The-Open-Memory-Initiative-OMI/omi/docs/how_omi_is_engineered.md

<!-- SPDX-License-Identifier: CC-BY-SA-4.0 -->
# How OMI Is Engineered

OMI (Open Memory Initiative) is not just an open hardware project.
It is an attempt to engineer memory systems **the way they should have been engineered all along**.

This document explains:
- How OMI approaches DDR memory design
- Why the process looks "heavy" before any PCB is drawn
- What kind of contributors OMI is built for
- Why correctness, not performance, is the first milestone

If you have ever debugged a memory issue that "shouldn't happen," this is for you.

---

## The Problem with How Memory Is Usually Designed

Most memory designs fail in one of two ways:

1. **They start with schematics too early**
2. **They rely on experience instead of explicit intent**

This leads to designs where:
- Architecture is implicit
- Constraints are tribal knowledge
- Layout decisions silently redefine behavior
- Failures appear late and intermittently
- Debugging becomes guesswork

Commercial teams survive this with time, money, and iteration.
Open projects usually don't.

OMI exists to change that.

---

## OMI's Core Belief

> **Memory correctness is architectural, not procedural.**

You cannot "fix" a bad memory design with:
- better routing
- more decoupling
- aggressive calibration
- luck

You can only prevent failure by **deciding correctly early** and **preserving those decisions relentlessly**.

---

## How OMI Is Different

OMI is engineered **from the outside in**, not the inside out.

Instead of:
> schematic → layout → debug → patch

OMI follows:
> system intent → architecture → constraints → implementation → validation → hardware

Every stage exists to **protect the previous one**.

---

## The OMI Engineering Stack (High Level)

OMI is structured into explicit stages:

### Stage 1–4: System Understanding
- Why DRAM behaves the way it does
- Memory hierarchy assumptions
- DRAM internals, protocols, and physics
- Signal integrity fundamentals

No design happens here.
Only understanding.

---

### Stage 5: Architecture
- Signals are defined
- Topologies are chosen
- Constraints are declared
- Power domains are separated
- Assumptions are locked

This is where *truth is defined*.

---

### Stage 6: Implementation Translation
- Architecture becomes structure
- Blocks, interfaces, and pin groupings are defined
- Nothing new is invented
- Nothing is optimized

This stage exists so schematics cannot lie.

---

### Stage 7: Schematic Capture Discipline
- How schematics must be drawn
- How intent must be visible
- How ambiguity is prevented

This stage exists because schematics are where most designs start to rot.

---

### Stage 8: Validation & Review
- Architecture compliance checks
- Schematic correctness checks
- Constraint enforcement
- Power and failure containment reviews

If a failure cannot be explained, the design is rejected.

---

### Stage 9: Minimal Reference Schematic
- One rank
- No optimizations
- No optional features
- Fully reviewable
- Fully correct

This proves the architecture is real.

---

### Stage 10: Layout & SI/PI Guidelines
- How physics must behave
- How layout must respect architecture
- How margins are preserved

No numbers. Only intent.

---

## What OMI Is *Not*

OMI is not:
- A fastest-memory project
- A cost-optimized DIMM
- A vendor replacement
- A shortcut to production hardware

OMI is a **reference-quality foundation**.

Performance, optimization, and productization come later — on top of something solid.

---

## Who OMI Is For

OMI is for engineers who:

- Have debugged memory issues they didn't cause
- Are tired of "it works on our board"
- Care about explainability more than heroics
- Want to contribute to something *structurally correct*
- Believe open hardware deserves the same rigor as closed hardware

OMI is not beginner content.
But it is honest content.

---

## How You Can Contribute

You can contribute to OMI by:

- Reviewing architectural documents
- Challenging assumptions
- Improving clarity without adding complexity
- Extending later stages carefully
- Helping translate the reference design into variants

You don't need permission to think critically.
You do need discipline to respect the process.

---

## The OMI Promise

OMI promises that:

- Every decision is documented
- Every constraint is visible
- Every failure is explainable
- Nothing important is implicit

If OMI succeeds, it won't just produce a DIMM.

It will produce a **way of engineering memory that others can trust, reuse, and build on**.

---

## Final Thought

Most hardware projects fail quietly.
Most memory bugs are never truly understood.

OMI is an attempt to do something harder:

> **Build memory systems that make sense — even years later.**

If that excites you, welcome.
