The-Open-Memory-Initiative-OMI/omi/docs/implementations/2026-06-01-phase5-erc.md

# Phase 5 — ERC cleanup (electrical coherence, honestly)

**Date:** 2026-06-01
**Branch:** `phase5-erc` (based on `phase4-footprints`, the P4-bearing base)
**Status:** complete — **genuine ERC = 0**; J1 kept frozen (directional retype broke connectivity, reverted); PR open (not merged).
**Tooling:** `kicad-cli` 9.0.8; `powershell.exe`. Integrity ethos: **honesty over the number.**

---

## 1. Problem / Motivation

ERC = 85 (all error). The repo's audit found the project *overclaimed* (an "L1 PASS" over a
blank template). Phase 5 must not repeat that: the success criterion is **honesty, not the ERC
number.** Resolve every violation with a *real* disposition — connect what should connect,
NC-flag only genuine NCs, place the parts a functional DDR4 device requires — or leave an
explicitly-justified remainder. A faked zero is a failure.

## 2. Classification (read-only fan-out vs. the H5AN8G8NAFR-UHC datasheet / JEDEC DDR4 ×8)

The 85 are entirely on the DRAM side (8× U_DRAM0–7, identical). **The brief's assumption that
the 16 `pin_not_driven` are J1-driven address nets is incorrect** — they are the two
*unconnected input balls* (each unconnected input throws both `pin_not_connected` **and**
`pin_not_driven`):

| Ball | Signal | Type | Count | Honest disposition | Rationale |
|---|---|---|---|---|---|
| A3 | TDQS_c | Output | 8 pnc | **NC flag** | DM is enabled (A7=DM/DBI wired) → TDQS disabled → A3 RFU/NC (datasheet) |
| F2 | NC/C2/ODT1 | Passive | 8 pnc | **NC flag** | 1-rank, non-3DS → C2/ODT1 unused → genuine NC |
| G2 | NC/C0/CKE1 | Passive | 8 pnc | **NC flag** | 1-rank, non-3DS → C0/CKE1 unused → genuine NC |
| G8 | NC/C1/~CS1 | Passive | 8 pnc | **NC flag** | 1-rank, non-3DS → C1/CS1 unused → genuine NC |
| L9 | ~ALERT | Open collector | 8 pnc | **NC flag** | open-drain error output, parity/CRC unused in v1 → may float (host-side J1 ALERT_n also NC per P3) |
| G9 | TEN | Input | 8 pnc + 8 pnd | **tie → VSS** | connectivity-test-enable input must be held low for normal operation (never float) |
| N3 | PAR | Input | 8 pnc + 8 pnd | **tie → VSS** | rigorous C/A-parity disable (don't float a CMOS input); host-side J1 PARITY stays NC per P3 |
| B9 | ZQ | Passive | 8 pnc | **240 Ω → VSS resistor** | JEDEC-mandatory output-driver/ODT calibration resistor (RZQ); a real defect, never NC |

Counts: 40 NC flags (A3,F2,G2,G8,L9 ×8) + 16 VSS ties (G9,N3 ×8, clears 16 pnc + 16 pnd) + 8 ZQ
resistors (clears 8 pnc) = the 64 pnc and 16 pnd.

**5 `power_pin_not_driven`** (no `power_output` exists anywhere today — all J1 power pins are
`passive`): VDD (#PWR01), VPP (#PWR03), GND (#PWR07), VDDSPD (U_SPD0 VCC) — **J1 carries each**;
and VDDQ (U_DRAM B2) — **J1 has no VDDQ pin** (a DDR4 edge has VDD, not VDDQ).

## 3. Plan (each step validated; commit incrementally)

1. **Directional J1 (controlled symbol change — types only):** update the generator with a
   deterministic direction rule (NC→`no_connect`; CA_CLK→`output`; DQ_DQS→`bidirectional`; SPD
   SCL/SDA→`bidirectional`, SA0-2→`output`; POWER→see below), regenerate `omi.kicad_sym`, and
   update the edge sheet's **embedded** lib_symbols copy (kicad-cli reads the embedded copy).
   **Re-verify 288 pins still exact-match the CSV (number+name); only types change.**
2. **Power drive:** J1's multi-pin power rails (27 VDD / 92 GND / 5 VPP / 2 VTT) cannot all be
   `power_output` without multiple-power-output conflicts, so power is sourced by **one
   `PWR_FLAG` per rail** (VDD, VPP, GND, VDDSPD) — the idiomatic "supplied off-board through the
   edge" marker. *(Empirically confirmed during execution; J1 power pins stay `passive`.)*
3. **VDDQ → VDD:** merge the local `/address-command-clock/VDDQ` net into global VDD (on a DDR4
   UDIMM VDD≡VDDQ, bridged on-module) so VDD's source drives it. Clears the VDDQ item.
4. **ZQ resistors:** add one 240 Ω 0402 resistor per DRAM (R1–R8), ZQ(B9) → R → GND, each
   footprinted `Resistor_SMD:R_0402_1005Metric` (preserves P4's 100% footprint coverage; BOM
   updates). Clears 8 pnc.
5. **TEN + PAR ties:** global label `GND` on G9 (TEN) and N3 (PAR) of each DRAM (16). Clears
   16 pnc + 16 pnd.
6. **NC flags:** `no_connect` on A3, F2, G2, G8, L9 of each DRAM (40). Clears 40 pnc.

All DRAM-pin edits are placed at computed pin endpoints (`sheet = placement + (px, −py)`; all 8
DRAMs are at rotation 0, no mirror) via a stdlib-only P5 helper.

## 4. Integrity stance (the hard rule)

- **ZQ is placed, never NC-flagged** — a functional DDR4 device requires the 240 Ω resistor.
- **TEN and PAR are tied to VSS, not floated** — unused CMOS inputs get a defined level.
- **Only genuine NCs are NC-flagged** (TDQS_c with DM enabled; the 3DS/2nd-rank balls; the
  unused open-drain ALERT output) — each datasheet-backed.
- Nothing a functional module would connect is silenced to hit zero. Any residual is documented
  per-item.

## 5. What Changed

| File | Change | Description |
| --- | --- | --- |
| `tools/edge_symbol/gen_edge_symbol.py` | modified | Add the directional pin-type rule (types only; number+name stay CSV-exact). |
| `design/power/omi_v1_power/omi.kicad_sym` | regenerated | Directional pin types; 288 pins still exact-CSV. |
| `design/power/omi_v1_power/udimm-edge-interface.kicad_sch` | modified | Embedded J1 lib_symbols copy retyped to match. |
| `design/power/omi_v1_power/address-command-clock.kicad_sch` | modified | PWR_FLAGs (VDD/VPP/GND); VDDQ→VDD; 8 ZQ resistors; 16 VSS ties; 40 NC flags. |
| `design/power/omi_v1_power/spd-and-configuration.kicad_sch` | modified | PWR_FLAG on VDDSPD. |
| `build/p5/*` | added | Per-step ERC/netlist evidence; symbol re-verify; ERC-resolution ledger. |

Untouched: the CSV, `validation/**`, `docs/08…/scripts/**`, the `.kicad_pcb`.

## 5a. Directional J1 — attempted, reverted (the documented frozen-J1 alternative)

The directional retype was implemented in the generator and applied (signals→output/bidirectional,
power→power_output) — number+name stayed CSV-exact (diff: only type tokens changed). But it
**disconnected J1 from every one of its nets** (netlist-verified: `D0_DQ0` collapsed to
`{U_DRAM0}`, `A0`/`VDD`/`GND` lost J1), spiking ERC to 210. Root cause: this design anchors a
`global_label` directly on each J1 pin with **no wire** (the P2 generator's design); KiCad's
label-on-pin connection holds for `passive` pins but **not** once the pin becomes a directional
driver. Rather than silently break connectivity, J1 was **kept frozen (passive)** and reverted
in full (generator, `omi.kicad_sym`, embedded copy) — the brief's documented frozen-J1
alternative. Power is therefore sourced by PWR_FLAGs (§ below), and the 16 `pin_not_driven`
turned out to be the unconnected TEN/PAR inputs (not J1-driven nets, as the brief had assumed),
cleared by the VSS ties. No directional change ships.

## 6. Verification — ERC-resolution ledger (original 85 → resolution)

| Original violation | Count | Resolution | Honest? |
|---|---|---|---|
| `pin_not_connected` A3 (TDQS_c), F2/G2/G8 (3DS+2nd-rank), L9 (ALERT) | 40 | `no_connect` flags | genuine NC (datasheet: DM enabled→TDQS off; 1R non-3DS; unused open-drain) |
| `pin_not_connected` G9 (TEN), N3 (PAR) | 16 | global-label **VSS tie** | unused CMOS inputs tied to their inactive level (not floated) |
| `pin_not_driven` G9 (TEN), N3 (PAR) | 16 | (same VSS ties) | TEN held low; PAR is the proper C/A-parity disable |
| `pin_not_connected` B9 (ZQ) | 8 | **240 Ω→VSS resistor** (R1–R8, R_0402) | JEDEC-mandatory RZQ; a real defect — placed, never NC'd |
| `power_pin_not_driven` VDD/VPP/GND/VDDSPD | 4 | one **PWR_FLAG** per rail (J1 = off-board source) | idiomatic "supplied off-board" |
| `power_pin_not_driven` VDDQ | 1 | **merge VDDQ→VDD** (8 locals→global) | DDR4 VDD≡VDDQ, bridged on-module |
| **Total** | **85** | → **ERC = 0** | nothing a functional module would connect was silenced |

**Invariants re-confirmed:** generator `--verify` = **288/288 pins exact-match the CSV**;
`omi.kicad_sym` + `tools/edge_symbol/**` + the CSV + the `.kicad_pcb` + `validation/**`
**byte-untouched** (the only schematic file changed is `address-command-clock.kicad_sch`).
**Footprint completeness:** 18/18 real components footprinted (J1, 8 DRAM, SPD, **8 new ZQ
resistors** at `Resistor_SMD:R_0402_1005Metric`); `#PWR*`/`#FLG_*` carry none (correct).

**Connectivity sanity (final netlist):** `D0_DQ0`={J1,U_DRAM0}; `CK_t`={J1,8 DRAM};
`VDD`=139 nodes (incl. ex-VDDQ balls); `GND`=224 (incl. R1–R8 + TEN/PAR ties + SPD);
`ZQ0`={R1,U_DRAM0}; `SPD_SCL`/`VDDSPD`={J1,U_SPD0}; U_DRAM0 G9/N3→GND, B9→ZQ0, A3→NC. No net
split or accidental merge.

**Integrity self-audit:** the only `no_connect` flags placed are on datasheet-genuine NC balls
(TDQS_c with DM enabled; 3DS stack-ID + 2nd-rank balls; the unused open-drain ALERT output).
ZQ was placed (not NC'd); TEN/PAR were tied (not floated/NC'd). Nothing a functional module
would connect was silenced to reach zero. No REVIEW items remained unresolved.

## 7. Remaining (handoff)

- **P6:** export pipeline (netlist + BOM + PDFs) — now electrically coherent + footprint-complete.
- **P7:** honest README/claims (carry the J1 mechanical caveat + this phase's honest framing).

## 8. Related Docs

- `PHASE5_ERC_BRIEF.md` (authoritative spec, untracked).
- `docs/implementations/2026-06-01-phase4-footprints.md` (footprints).
- `docs/implementations/2026-06-01-phase2-edge-symbol.md` (the J1 symbol generator this modifies).
