The-Open-Memory-Initiative-OMI/omi/docs/01_dram_fundamentals/destructive_reads.md

# Destructive Reads: Why Reading DRAM Alters Its State

This document explains **why reading DRAM is inherently destructive**, how this behavior shapes timing constraints, and why correct restoration is essential for system reliability.

Destructive reads are one of the most important differences between DRAM and other memory technologies.

---

## What "Destructive Read" Means

In DRAM, a read operation does not merely observe stored data.

It **changes the physical state** of the memory cell.

Specifically:

- Reading a DRAM cell discharges or redistributes its stored charge
- The original data is disturbed in the process
- The cell must be rewritten to preserve correctness

This behavior is fundamental to DRAM operation.

---

## Why Reads Are Destructive

DRAM cells store data as extremely small amounts of charge.

When a row is activated:

- Each cell connects to a bitline
- Charge flows from the capacitor to the bitline
- The voltage difference is sensed and amplified

This process necessarily:

- Draws charge out of the cell
- Collapses the original stored state

There is no way to sense the charge without disturbing it.

---

## Sense Amplifiers as Restorers

Sense amplifiers serve a dual role:

1. Detecting the stored value
2. Restoring the value back into the cell

Once amplification occurs:

- The sensed value is driven strongly
- The capacitor is recharged or discharged fully
- The original data is rewritten

This restoration happens **while the row remains active**.

---

## Why Timing Matters During Restoration

Restoration is not instantaneous.

It requires:

- Sufficient time for amplification
- Stable power and reference voltages
- Minimal noise and disturbance

If timing is shortened:

- Restoration may be incomplete
- Charge levels may be marginal
- Data may decay faster than expected

Errors may not appear immediately.
They may surface minutes or hours later.

---

## Relationship to Precharge

After a row is accessed:

- It must be closed (precharged)
- Bitlines must return to a neutral state
- Cells must be isolated again

Precharge is required to:

- Prepare the array for the next activation
- Prevent interference between rows
- Maintain charge integrity

Skipping or shortening precharge corrupts data.

---

## Why Partial Reads Are Not Possible

Because an entire row is activated:

- All cells in the row are disturbed
- Even if only a few columns are read

This means:

- Every read is effectively a read-modify-write operation
- Restoration happens for the entire row
- Timing parameters must protect all cells

This is why DRAM accesses are fundamentally row-based.

---

## Interaction with Refresh

Refresh and reads are closely related.

- A refresh operation is effectively an internal read and restore
- Normal reads also perform restoration
- Both depend on the same physical mechanisms

Incorrect read timing affects refresh reliability, and vice versa.

---

## Why Errors Can Be Delayed

A destructive read error may:

- Slightly under-restore charge
- Leave data barely within margin
- Pass immediate verification

But:

- Subsequent leakage accelerates decay
- Later reads observe corrupted data
- Failures appear disconnected from cause

This delayed manifestation makes debugging extremely difficult.

---

## Implications for DDR Timing Parameters

Several DDR timing parameters exist **solely** because reads are destructive:

- Row active time (ensuring full restoration)
- Precharge time (ensuring safe isolation)
- Activate-to-read delays
- Read-to-precharge constraints

These timings protect data integrity, not performance.

Violating them risks silent corruption.

---

## Why This Matters for Module-Level Design

At the module level:

- Signal integrity affects sensing accuracy
- Power noise affects amplification
- Timing skew affects restoration completeness

Design margins exist to ensure destructive reads do not become destructive failures.

OMI documents these relationships explicitly.

---

## Why Destructive Reads Are Often Ignored

Many engineers never encounter this concept because:

- DRAM abstracts it away
- DDR protocols enforce safety automatically
- Failures are rare and silent

But ignoring it leads to:

- Misinterpretation of timing rules
- Overconfidence in marginal designs
- Fragile systems

---

## Takeaway

DRAM reads are not passive.

Every read:

- Destroys stored charge
- Relies on precise restoration
- Depends on timing, power, and signal quality

Correct memory operation exists only because these destructive effects are carefully controlled.

OMI exists to make those controls visible and understandable.
