The-Open-Memory-Initiative-OMI/omi/CHARTER.md

<!-- SPDX-License-Identifier: CC-BY-SA-4.0 -->
# The Open Memory Initiative (OMI) 

#  An Open, Community-Built DDR Memory Initiative

## 1\. Executive Summary:

While modern computing systems depend on DRAM, memory in particular is still one of the most closed and least understood parts of a system’s system stack. Even though processors and toolchains (and perhaps accelerators) are moving in a positive direction in open-source terms and making meaningful headway, system memory is yet to become commonplace with obscure designs, lack of knowledge, as well as a barrier to independent implementation being among the top reasons behind it. That has bred a structural imbalance. Open CPUs and open systems continue to rely on closed memory. Education focuses on using memory rather than understanding or building it. AI-driven demand and supply constraints, alongside market prioritization, have revealed the fragility and centralization of the memory ecosystem.

The OMI Project attempts to fill this gap. OMI is a community-driven initiative to develop open, reproducible, and manufacturable DDR memory module design from mature DDR technology, building upon PC DIMMs. Initially, a complete approach toward module-level design is accomplished, i.e. schematics, PCB layouts, documentation, and validation methodology before any chip-level DRAM design. 

OMI is a very strict definition of openness. All design artifacts and documentation, test procedures, and decision rationales must be publicly available. No closed IP, NDA-gated knowledge, or black-box components are allowed. If a design cannot be studied, reproduced, and independently verified, it fails to meet the criteria. The initial scope is deliberately limited. 

OMI v1 aims to develop a single, well-documented DDR module that can be constructed and tested on classical PC hardware. Success is not defined by performance leadership or commercial adoption, but by reproducibility, clarity, and independent verification. 

OMI is not marketed as a direct competitor to those memory makers. It is an enabler which closes the gap from open computing stack to repair the knowledge gap, and form the basis for future research, education, and experimental work. The project is successful only when many can use it and continue to build on it without permission from someone else.

## 2\. The Problem:

Why Memory Is Gatekept. DRAM is crucial to modern-day computing, yet it is still one of the least accessible and opaque technologies in the semiconductor industry. No, it’s not a coincidence of complexity. It is the result of intentional structural decisions that concentrate knowledge, capacity, and power in the hands of very few actors.

### 2.1 Market Concentration and Artificial Scarcity:

The world’s DRAM market is dominated by a tiny number of manufacturers. This sort of concentration builds a brittle ecosystem where supply decisions are also centralized, opaque, and governed by the whims and preferences of few; not the general computing community. In recent years, we have observed:

Repeated shortages of DRAM which have nothing to do with physical manufacturing limitations. Uncorrelated price volatility regardless of raw material and process changes. The systematic prioritization of high-margin markets, for example, AI accelerators and data centers. Consumer PCs, developer machines, and education platforms are deprioritized. Such dynamics have real impacts. Developers, students, researchers, and independent builders experience increasing costs and declining access to a component crucial to basic computing in the modern era. That scarcity here is not only technical. It has an organizational dimension.

### 2.2 Closed IP and Licensing Barriers:

Although DDR standards are officially published, participation in DRAM design is significantly stymied by a complex interplay of intellectual property and licensing constraints. Key barriers include: Critical implementation details obscured by NDAs. References available exclusively as proprietary designs without public access. Patent portfolios that render independent implementation legally risky. Toolchains and validation flows accessible only through commercial agreements. So “open” tends to mean: You can interpret the specification. You may not build from it. That leads to a one-way dependency; where engineers are trained to consume memory, integrate memory, and optimize around memory, but not to design memory.

### 2.3 Knowledge Hoarding in DRAM Design:

The knowledge on the design of DRAM does not flow freely through universities, open literature, or community projects. Rather, it is siloed within companies and protected as a competitive advantage. This leads to: A growing disconnect between academia and industry. Little publicly available, end-to-end DRAM design cases. Lack of open reference implementations. A dwindling body of engineers who see memory beyond the interface level. The result is structural fragility. When knowledge fails to trickle down, systems become dependent on institutions rather than understanding.

### 2.4 The Consequence: A Broken Feedback Loop:

In healthy engineering ecosystems: Knowledge is transmitted from the industry to education. Education creates new engineers. Engineers develop alternatives and new possibilities. This loop has been broken by today's memory ecosystem. Without open memory:

Open CPUs remain incomplete. Closed components still power open systems. Hardware education continues to be abstract. Innovation remains centralized. This is not sustainable for open computing, long-term resilience, or technological sovereignty.

## 3\. Why Open-Source RAM Is Necessary Now:

Open-source hardware is no longer experimental. It’s already redesigning CPUs, accelerators, interconnects, and full system-on-chip ecosystems. But memory, the bedrock of all computation, remains closed. This has turned into an asymmetry that is structural. The need for open-source RAM is no longer theoretical or aspirational. It is immediate.

### 3.1 Open Computing Cannot Exist Without Open Memory:

Open instruction sets and open processor designs have been demonstrated in the past decade as viable. Open CPUs have been built, verified, and shipped at scale by communities and companies. However, these systems still use opaque memory components.

Without open memory:

Open CPUs remain dependent on closed subsystems. Transparency at the system level is broken at the most fundamental layer. Debugging, optimization, and education stop at the memory interface. An open system will not ever be open if its most central aspect is not being studied, modified, or rebuilt. Open-source RAM is not an addendum to open hardware, it’s an essential prerequisite.

### 3.2 AI-Driven Demand Has Exposed Structural Fragility:

The exponential growth of AI workloads has tilted global DRAM allocation toward an almost exclusive user pool of high-margin customers. This has worsened existing vulnerabilities in the memory supply chain.

The impacts are already felt:

* Consumer and developer hardware is deprioritized. Prices and availability rise and fall unexpectedly. Memory becomes a strategic resource rather than a commodity.  
* When a foundational technology runs into strategic scarcity, openness is no longer a philosophical position; it is a strategy for resilience.

Open memory designs create:

1. Alternatives to centralized supply decisions.   
2. Transferable knowledge to other regions and institutions.   
3. The possibility of localized or diversified manufacturing.

### 3.3 Education and the Disappearance of Memory Expertise:

Memory systems are extensively taught at the interface and almost never at the actual implementation level.

Today most engineers graduate armed with used DDR memory, Tuned memory controllers and Modeled memory performance.

But having never designed a memory module or understood real signal integrity constraints. Worked through validation and bring-up…

This is not because there is no interest or capability in these areas. It is due to lack of access. An open source RAM project would restore the missing educational layer: actual, buildable, inspectable hardware.

### 3.4 Timing: Why This Is the Right Moment:

Three conditions now exist in parallel:

1. Mature DDR generations. DDR3 and DDR4 are widely supported, stable, and well understood.  
2. Open hardware momentum. PCB manufacturing, toolchains, community collaboration, etc. are more accessible than ever.  
3. Clear system-level demand. Developers, academics, and trainees all need transparency, not just performance.

A combination of these factors makes an open RAM project both practical and meaningful. This is not to disturb cutting-edge DRAM manufacturing. It is an assertion of re-establishing awareness at an elemental level.

### 3.5 This Is Not About Competing. It Is About Completing:

OMI is positioned not to compete with other producers. Instead, it exists to complement open CPUs. Strengthen open systems. Extend the network of engineers who have a profound understanding of memory.   
The objective is not to compete with industry. The point is to make memory no longer a single point of opacity in otherwise open systems.

## 4\. Design Philosophy & Core Principles:

OMI not only builds what it builds, but how it builds in addition to why. The following principles are non-negotiable. These are meant to safeguard the project from dilution, disunity, and quiet closure.

### 4.1 Openness Is a Technical Requirement, Not a Preference:

In this project, “open” has a strict meaning.

All artifacts necessary to comprehend, reproduce, validate, and adapt to the system must be publicly available. This includes, but is not limited to:

1. Electrical schematics  
2. PCB layouts and stack-ups  
3. Bill of materials  
4. Design constraints and assumptions  
5. Test methods and validation results  
6. Design dialogues and rationale of decisions

If a component or process cannot be documented without violating an NDA, it does not belong in the OMI stack. 

Partial openness is not openness\!\!\! 

Documentation without buildability is not openness\!\!\!

### 4.2 No Black Boxes:

They explicitly reject black boxes.

Any element that requires:

1. Trust without verification  
2. Vendor-only knowledge  
3. Undisclosed internal behavior

is incompatible with this project’s objectives.

All design decisions should be explainable\! All interfaces must be traceable\! Every limitation must be documented\! Complexity is acceptable. Opacity is not\!

### 4.3 Engineering First, Hype Last:

OMI values correctness, reproducibility, and clarity over speed, marketing, or perceived innovation.

This means:

1. Working hardware matters more than announcements  
2. Measured results matter more than projections  
3. Failed experiments are documented, not hidden  
4. The project advances through evidence, not persuasion.

### 4.4 Buildable by Others:

A design that only its creators can build has failed. All OMI outputs must satisfy the following condition:

A competent engineer, with access to standard tools and public documentation, must be able to reproduce the design and results.

This principle governs; Component selection, Manufacturing assumptions, Testing environments and documentation depth.

If a design cannot be independently rebuilt, it is incomplete\!

### 4.5 Incremental, Layered Progress:

OMI progresses in deliberate layers:

1. Understanding  
2. Documentation  
3. Design  
4. Validation  
5. Iteration

Skipping layers introduces hidden debt.  
Each layer must stand on its own before moving forward.

This approach favors long-term stability over short-term progress.

### 4.6 Decisions Follow Evidence, Not Authority:

Design decisions are justified on technical grounds — not seniority, affiliation, or assertion.

Decisions are made based on:

1. Technical merit  
2. Evidence  
3. Reproducibility

A decision stands because it can be defended and reproduced, not because of who made it.

### 4.7 Transparency Includes Limitations:

OMI documents not only what works, but also:

1. What does not work  
2. What is not yet understood  
3. What remains unresolved

Uncertainty is treated as engineering data, not weakness.

## 5\. Why Start with PC DDR Memory:

OMI starts with PC DDR memory by design, not convenience. The decision is made to strike a conscious balance between technical feasibility, community accessibility, and real-world impact. Beginning elsewhere would prolong execution indefinitely or limit it to a select group of specialists.

### 5.1 Why DDR (and Not SRAM, HBM, or LPDDR):

Dynamic RAM is the dominant form of main memory in general-purpose computing. Any serious attempt to open the memory stack must eventually address DRAM.

Within DRAM technologies, DDR is the most sensible starting point for these applications:

1. DDR3 and DDR4 are mature and well-characterized  
2. There are numerous tooling and measurement equipment for DDR  
3. Platform support from CPUs and chipsets is extensive  
4. Challenges in signal integrity are complex but tractable

By contrast; SRAM does not model the memory used to create the system at scale, HBM brings with it packaging, interposer, and IP limitations, LPDDR is intimately linked with SoC vendors and mobile ecosystems.

DDR strikes the balance between realism and accessibility.

### 5.2 Why PCs First:

Personal computers are the natural environment for open hardware development.

PC platforms offer:

1. Open firmware and BIOS ecosystems  
2. Documentation and community knowledge  
3. Probing, debugging, and testing for physical accessibility  
4. A large installed base for validation across varying configurations

First, PCs are where developers, researchers, and students already have jobs. 

By targeting PC DIMMs; Validation can happen with commodity hardware, failures can be examined without specialized labs, Industry partners are not alone in contributing.

Choosing OMI this way keeps OMI a community rather than an institutional project.

### 5.3 Why Module-Level Design Comes Before Chip-Level Design:

Having a DRAM chip as an ultimate goal is not the starting point of the process.

Module-level design offers:

1. Clear separation of concerns  
2. Close in time, for relevant participation  
3. Reduced legal and manufacturing hurdles  
4. A realistic way to actual physical prototypes

The project can, at the module level:

1. Record genuine electrical limitations  
2. Investigate signal integrity trade-offs  
3. Define the testing and validation practices  
4. Construct institutional knowledge that works upward

Attempting to start at the silicon level would put the risk, legal complication, and cost up front and delay the benefits before they are realized.

### 5.4 Alignment with Open Hardware Ecosystems:

Initiating with PC DDR, OMI is in tune with other open hardware initiatives on offer today.

It allows:

Open CPU platform compatibility  
Applications in open-source system builds  
Adoption in academic and research environments

This alignment enhances relevance while reducing overreliance on proprietary ecosystems

### 5.5 Practical Impact from Day One:

A PC DDR module is not one of the demonstration artifacts. It is an actual, deployable component. Success at this level means:

1. The design can be manufactured  
2. The design can be deployed to regular systems  
3. It can be tested in real workloads

This means OMI is yielding outputs, not abstractions.

## 6\. Scope Definition \- Version 1: 	Uncontrolled expansion is the real danger to any ambitious open hardware project. OMI v1 is therefore marked out with strict boundaries. These boundaries, instead of being hindrances to vision, are checks on execution.

### 6.1 What Version 1 Includes:

OMI v1 is an entire design of a fully buildable and testable PC DDR memory module. The scope of v1 includes:

1. DDR3 or DDR4 (determined by community assessment of feasibility and tooling)  
2. Standard PC DIMM form factor  
3. Open electrical schematics  
4. Open PCB layout and stack-up  
5. An approach with documented design constraints and assumptions  
6. Bill of materials with accessible components  
7. Signal integrity issues and trade-offs  
8. Methodology for bringing up and validating  
9. Test results measured on physical hardware

Documentation of all design work put out by v1 must be sufficiently valid and sufficient for independent reproduction through external contributors.

### 6.2 What Version 1 Explicitly Excludes:

To stay in focus and in the groove, the following fall outside the scope of v1:

1. Mobile memory technologies (LPDDR)  
2. Server-specific memory formats  
3. High-bandwidth memory (HBM)  
4. Custom DRAM chip fabrication  
5. Process nodes that are advanced or bleeding-edge  
6. Proprietary IP blocks or licensed reference designs  
7. Closed or NDA-gated tooling

These exclusions are done intentionally. Each has dependencies or restrictions that oppose the open and accessible objectives of the project.

### 6.3 Why the Chip Comes Later:

Version 1 does NOT seek to design a DRAM chip.

This is a technical and legal reality. DRAM cell and sense amplifier design are heavily patented. The fabrication requires access to specialized foundries. Also the verification costs scale non-linearly at the silicon level. Therefore starting at the module level, OMI builds a foundation for electrical understanding, validation discipline, community experience… In short, the scope is an essential precursor to any silicon work of the future.

### 6.4 Criteria for Expanding the Scope:

It is not only ambition that drives scope expansion.OMI v1 will continue to expand only if:

1. This design is buildable and validated  
2. Documentation is complete  
3. Results can be verified by multiple independent contributors

Only then will the project look at:

1. Additional DDR generations  
2. Alternative form factors  
3. Some preliminary chip-level research

### 6.5 Scope Discipline as a Design Principle:

Every contribution is assessed against v1 scope. If a proposal:

1. Delays validation  
2. Introduces closed dependencies  
3. Increases legal or manufacturing risk

It does not belong in v1.

This discipline guarantees that OMI works through completion rather than accumulation.

Version 1 serves to show that open memory actually exists in practice, rather than just as a thought experiment in theory.

## 7\. Technical Deliverables:

OMI consists of outputs. The project does not measure progress by talk or intent but by the tangible artifacts that others can inspect, build and validate. Each of the deliverables in this section should be considered a first-class engineering result. Partial documentation or unpublished results are unfinished work.

### 7.1 Design Artifacts:

The project will lead to a full set of design artifacts, necessary for the manufacture of a PC DDR memory module. This covers complete electrical schematics detailing all functional connections, power delivery, termination and control signals. The explanations that follow design intent and assumptions should be included with each schematic.

We will publish printed circuit board layouts in native design formats and in highly readable export formats. Explicit documentation of layer stack-ups, trace geometries, impedance targets, and routing constraints. All trade-offs during layout shall be documented and justified.

A complete bill of materials is kept. Components must be commercially accessible without special contractual terms. And where they do exist, the alternatives need to be explained and explain their performance or manufacturability consequences.

### 7.2 Documentation and Design Rationale:

Documentation is considered part of the design, not a secondary artifact. It should be accompanied each major design choice with written rationale. Component selection, topology choices, termination strategies, and layout constraints fall into this category. Here the objective is not to tell only what was done but to explain why it was done.

All assumptions to be expressed plainly. Conditions regarding the environment, platform dependencies and operating margins must be clearly documented such that other researchers can replicate the results under similar circumstances. If any of them are not clear-cut, the ambiguity should be documented properly. OMI is as much about transparency of limitations as correctness of implementation.

### 7.3 Validation and Testing:

Validation is a primary deliverable, not afterthought. The project will define clear bring-up and testing steps that can be run on standard PC devices. These steps should be described through a detailed description of tools needed, firmware settings, and measurement points.

Full test results will be published. Documentation of successful outcomes, marginal behavior, and failures. If a test does not perform according to expectation, the investigation process and results must be logged. Validation should be considered complete only when independent contributors reproduce the results with the published documentation.

### 7.4 Iteration and Revision Tracking:

OMI assumes a first prototype won’t be right. Any changes have to be publicly documented. The revisions should be recorded, with explicit explanations as to what was changed and why. And the regression testing results for each revision should be accompanied where necessary. This method ensures that all of the progress is cumulative and that lessons learnt are preserved rather than lost.

## 8\. What Success Looks Like:

OMI success is about completion not visibility. It does not set itself up to optimize for announcements, adoption metrics, or outside validation. It optimizes to whether the work can survive alone, and be used by others. The twelve-month timeline is there for discipline, not urgency. It sets an achievable horizon in which the project must prove that open memory is possible.

### 8.1 Minimum Viable Success:

At the end of 12 months, OMI has been successful if the following criteria are reached.

* There is a public specification published which details the design, assumptions, and constraints of a PC DDR memory module.  
* All design artifacts necessary to produce the module are published and versioned. This data includes schematics, PCB layouts, stack-up information, and a verified bill of materials.  
* The module design has been physically manufactured and installed in standard PC systems. Basic bring-up and operation conditions have been demonstrated under documented conditions.  
* The validation and test results are publicly available. We present results both of successful operation and of identified limitations.  
* At least one independent contributor beyond the original authorship has reproduced part or all of the work with published materials.

> **Current status (schematic milestone reached).** OMI v1 now has a complete,
> **ERC-clean** DDR4 UDIMM schematic: a real 288-pin edge connector, full
> footprint assignment, and generated netlist/BOM/PDF (see the repository
> `README.md` → Project Status, and `exports/`). The remaining Minimum Viable
> Success criteria above — a **physically manufactured** module, **bench bring-up**,
> and **measured results on real hardware** — are **not yet met**; they remain
> future/aspirational work beyond the current schematic scope. This charter states
> the destination; it does not claim that fabricated, tested hardware exists today.

### 8.2 Quality Over Breadth:

Success is not dependent on multiple form factors, multiple DDR generations, or extensive platform coverage.

One clear documented, reproducible, and validated design is far more useful than many partial or unverified designs.

Completeness is prioritized over expansion.

### 8.3 Stretch Outcomes:

Though they do not need to be part of the core work to succeed, the following are relevant builds on the idea.

* Multiple design revisions with documented lessons learned to incorporate the experience.  
* Forks or modified designs in standalone forks or to adapt the design by external contributors.  
* Utilization of the OMI documentation in academic courses, research projects, and teaching laboratories.  
* Early exploratory work examining feasibility of future scope expansion without committing the project to it.

### 8.4 What Success Does Not Mean:

Success is not commercial adoption, mass production, or leadership position. They are not working to outperform proprietary memory products.

The objective is to make memory understandable, buildable, and open…

If OMI allows others to learn, to experiment, and to extend the work without permission, it has succeeded.

## 

## 

## 

## 9\. Governance and Contribution Model:

OMI is currently developed and maintained by a single author, in the open. It is built so that others can read, reproduce, challenge, and extend the work — not as a multi-stakeholder consortium. This section describes how the project is organized and how contributors can take part. "Governance" here means continuity and transparency — decisions recorded and justified so they can be audited — not committees or control.

### 9.1 Who Can Contribute:

OMI is there for everyone to contribute constructively and openly to get involved. The contributors can be engineers, researchers, students, educators, or independent hardware builders. Formal qualifications, institutional background, or previous work experience in the field of memory design does not have to be a prerequisite. The quality of contribution is important, not the identity of contributors.

### 9.2 Forms of Contribution:

OMI does not just depend on generating code and drawing schematics. Valid contributions are design work, documentation, testing, validation, simulation, failure analysis, tooling support, and review of existing work. When done constructively, identifying errors, gaps, or ambiguities is viewed as meaningful contribution. We trust everyone to have written up the contributions that they would benefit others by creating a paper trail of a document which can be shared with others.

### 9.3 Decision-Making Process:

Technical decisions are made on the record and justified on technical grounds. They are based on the available evidence, reproducibility, and alignment with the project's scope and principles. Where trade-offs exist, the option that minimizes risk, adds clarity, or preserves openness is preferred. Decisions and their rationale are documented so they can be audited and revisited later.

### 9.4 Maintenance:

The project is presently maintained by its author, who reviews contributions for consistency, correctness, and alignment with the charter's principles and scope. As the project grows, maintenance can be shared with sustained contributors. Maintainers are stewards of the project's principles, not gatekeepers of participation.

### 9.5 Transparency and Accountability:

All project work is in public view. This extends to design discussions, reviews, accepted changes, and limitations identified. Decisions have to be traceable. Rationales should be documented so future contributors know why choices were made. Mistakes are recognized candidly by way of any acknowledgment. Corrections are logged, not wiped out.

### 9.6 Code of Conduct:

OMI expects all participants to participate respectfully and professionally. Technical disagreement is encouraged. Personal attacks, harassment, and exclusionary behavior are not accepted. The project emphasizes that clarity, honesty, and mutual respect are of core value to effective engineering collaboration. See [CODE_OF_CONDUCT.md](CODE_OF_CONDUCT.md).

## 10\. Risks, Limitations, and Reality Check:

OMI is an ambitious technical project. Understanding risks and constraints early is necessary to preserve credibility and focus. There is an explicit scope to address constraints in this section rather than hidden ones later on.

### 10.1 Technical Risks:

Design and validation of DDR memory modules involve non-trivial electrical and system-level challenges. Signal integrity margins are narrow. The routing, impedance control, termination, and timing relationships must be correct under various operating conditions. Inconsistent or undetectable failures are produced by some small mistakes. Validation is heavy. Memory errors are not always deterministically produced, and failures might be determined by platform-specific behavior, firmware configuration, or environmental elements. Testing requires discipline. So with no rigorous and repeatable tests, they might appear to succeed but hide latent problems. The risks cannot be eliminated. Design, documentation, and validation will only manage them.

### 10.2 Tooling and Resource Constraints:

Whilst the project aims at being accessible, not all needed tools are easily accessible. Some devices with high quality measurement could include DDR signal analysis oscilloscopes which not everyone may have access to. Different platforms may also cause heterogeneities in validation results. OMI gets around this by documenting assumptions and tooling alternatives and known limitations in such methods, not by assuming homogeneity of capability across contributors.

### 10.3 Legal and Intellectual Property Awareness:

Memory technology also operates within a densely populated intellectual property landscape. OMI does not attempt to reverse engineer proprietary designs or to circumvent licensing constraints. The project avoids incorporating patented or NDA protected information and only focuses on publicly available knowledge and original solutions. This limitation may restrain some implementation decisions but is indispensable for the future sustainability and openness of the project. Contributors are also required to respect these boundaries and report uncertainty.

### 10.4 Scope and Time Constraints:

It’s by design the 12-month time horizon is hard. Projects driven by volunteers have to strike a balance between progress and availability of contributors. Work can be delayed and incomplete. This risk is reduced by firm controls over scope, incremental milestones, and definiteness of completion. OMI favors getting a narrow scope right over growing indefinitely.

### 10.5 Why This Is Still Worth Doing:

Notwithstanding such hazards, the decision is justified. Even partial success brings long lasting value. Documentation, design rationale, and validation methodologies remain useful independently of final hardware outcomes. In its own right, making memory design visible and discussable itself is a greater change than merely trying to produce a better version. OMI is not guaranteed to succeed. It is guaranteed to teach.

## 11\. Call to Action:

OMI is only here if we want to build it. This project doesn’t start with funding or money, institutional support or proprietary access. It starts with the engineers and researchers who believe that foundational technology is important. If you have ever used memory not having a chance to inspect, alter, or explain it from beginning to end, this project is for you.

### 11.1 Who We Are Looking For:

OMI wants contributors that deeply and responsibly engage with open memory. This is composed of electrical engineers, PCB designers, and signal integrity experts, as well as validation and test engineers, firmware developers, researchers, teachers, and students with a passion in technology. No previous experience with DDR is necessary. Willingness to be taught, to document in a manner that others will understand and discuss in the open.

### 11.2 What We Expect:

Contributors should operate transparently in their work. Meaning that they should document assumptions, display some intermediate results and treat the reviewers as part of the actual engineering process and treat review of their progress as part of doing something similar. It also involves respecting the project’s parameters; its scope, principles and legal limits. OMI values careful progress over rapid but fragile advances.

### 11.3 How to Get Involved:

Participation begins in public. Read the documentation. Review the existing material. Join the discussion channels. Find gaps, where there are gaps, if not areas where your knowledge fits. Start small if needed. Improve a document. Review a schematic. Replicate a test. Each solid contribution bolsters the project.

### 11.4 What This Project Offers:

OMI gives you no exclusivity and no entitlements. It offers something rarer. Open access to work on foundational hardware. An opportunity to provide knowledge to others to build off of, without permission. If the project does succeed, its founders will not own it. It will belong to the community that made it a reality. Open memory is not given. It is built. If you think memory should be understandable, reproducible and open, you can step up and help build it.

## 12\. Appendix:

### 12.1 Terminology and Definitions:

DDR (Double Data Rate): A family of synchronous dynamic random-access memory technologies used as main system memory in most general-purpose computers. 

DIMM (Dual Inline Memory Module): A standardized physical form factor for memory modules used in desktop and server systems. 

Module-Level Design: The design of the memory module as a system, including PCB layout, power delivery, routing, termination, and component selection, but excluding the internal silicon design of DRAM chips. 

Validation: The process of demonstrating that a design operates correctly under defined conditions using repeatable tests on real hardware. 

Open Hardware: Hardware whose design files, documentation, and test methodologies are publicly available and allow independent reproduction without proprietary restrictions.

### 12.2 Prior Art and Influences:

OMI does not emerge in isolation. It builds on decades of work across multiple domains. It’s inspired by open-source software movements that demonstrated the long-term value of shared infrastructure and transparent development. It is also informed by open hardware initiatives that have shown complex systems can be collaboratively designed and manufactured when scope and discipline are respected. The absence of a comparable effort in commodity memory is not due to lack of need, but due to historical barriers that this project explicitly addresses. 

### 12.3 Relationship to Standards Bodies:

OMI does not attempt to redefine or replace existing DDR standards. The project treats published standards as reference material while recognizing that standards alone do not constitute an implementation. Where standards leave ambiguity or omit practical detail, OMI documents the assumptions and interpretations used in its designs.

### 12.4 Legal and Ethical Boundaries:

OMI operates strictly within legal and ethical limits. The project does not solicit or accept NDA-protected information. Contributors are expected to avoid sharing proprietary designs, confidential documents, or patented implementations that cannot be freely redistributed. When uncertainty exists, the default action is to document the uncertainty and proceed conservatively.

### 12.5 Living Document Notice:

This charter is a living document. Revisions may occur as the project evolves, but changes must preserve the core principles defined in Sections 4 and 6\. Any substantial modification to scope, openness, or governance must be discussed publicly and justified clearly. The appendix may expand over time to include references, lessons learned, and historical context as the project matures.
