The-Open-Memory-Initiative-OMI/omi/docs/00_system_context/why_dram_is_critical.md

# Why DRAM Is Critical (and Why It Is Dangerous)

This document explains **why DRAM is the most critical and fragile layer** in the memory hierarchy, and why its opacity creates systemic risk in modern computing systems.

Understanding this is essential before attempting to design, document, or validate system memory.

---

## DRAM Is the Last Trusted Layer

From the system's perspective, DRAM is the **final layer of trust**.

Everything above it assumes:

- Data is stored correctly
- Reads return valid values
- Writes persist reliably
- Memory ordering rules are respected

Unlike storage, DRAM is not treated as unreliable.
Unlike caches, DRAM is not tightly controlled by the CPU.

Yet it supports:

- Running programs
- Operating system state
- Kernel data structures
- Application memory
- Security boundaries

If DRAM is wrong, *everything is wrong*.

---

## DRAM Errors Are Uniquely Harmful

Many system components can fail safely or visibly.

DRAM often cannot.

### Characteristics of DRAM failures:

- Silent data corruption
- Data-dependent behavior
- Temperature sensitivity
- Timing sensitivity
- Platform-specific manifestation
- Non-deterministic reproduction

A marginal condition may corrupt memory once per hour, once per week, or only under specific workloads.

From software's point of view, this looks like randomness.

---

## Why Software Cannot Defend Against Bad DRAM

Software assumes memory correctness by design.

Most programming models do not include:

- Verification of every memory load
- Redundant storage for all data
- Continuous integrity checks

Even when protections exist (such as ECC), they:

- Are not universally present
- Do not cover all failure modes
- Can mask underlying marginal behavior

As a result:

- Software bugs are blamed
- Hardware issues remain hidden
- Root causes are rarely identified

---

## DRAM Errors Propagate, Not Isolate

A corrupted value in DRAM does not stay local.

It can:

- Alter program control flow
- Corrupt file system data
- Break cryptographic guarantees
- Invalidate program logic silently

Once propagated, it becomes impossible to determine where the fault originated.

This is why memory correctness is **qualitatively different** from performance or efficiency.

---

## DRAM Is Physically Fragile by Nature

DRAM is not fragile because of poor engineering.
It is fragile because of physics.

Fundamental constraints include:

- Charge leakage
- Narrow timing margins
- Tight voltage tolerances
- High-speed signaling
- Analog behavior in a digital system

Correct operation exists within a **small, carefully engineered envelope**.

Violating that envelope does not always cause immediate failure.
It causes *uncertainty*.

---

## The Black Box Problem

Despite its critical role, DRAM is often treated as a black box.

Typical system-level visibility includes:

- Capacity
- Speed grade
- Nominal timings

Missing are:

- Design assumptions
- Electrical margins
- Validation conditions
- Known limitations
- Failure characteristics

This lack of transparency means:

- Engineers integrate memory they cannot inspect
- Educators teach abstractions without foundations
- Debugging ends at speculation

---

## Why This Is a Systemic Issue

As systems scale:

- Memory sizes increase
- Access patterns become more complex
- AI and data workloads stress memory continuously

At the same time:

- Knowledge of memory design is centralized
- Documentation is gated
- Implementation details are hidden

This creates a fragile ecosystem where a foundational component is both essential and opaque.

---

## Why OMI Starts Here

OMI does not begin with schematics or layouts.

It begins by stating something explicitly that systems quietly assume:

> DRAM must work correctly, and we must understand *why*.

By documenting:

- Assumptions
- Constraints
- Failure modes
- Design rationale

OMI aims to turn memory from a silent dependency into an understandable system component.

---

## Implication for the Project

Because DRAM errors are:

- Silent
- Destructive
- Difficult to reproduce

OMI treats:

- Documentation as a primary deliverable
- Validation as a core activity
- Transparency as a technical requirement

Memory that cannot be explained cannot be trusted.
Memory that cannot be reproduced cannot be validated.

---

## Takeaway

DRAM is not just another component.

It is the **foundation on which all computation quietly depends**.

Its failures are rare, subtle, and devastating.
Its correctness is assumed, not verified.
Its design is critical, yet hidden.

OMI exists to change that.
