The-Open-Memory-Initiative-OMI/omi/validation/evidence/probe_checklist.md

# OMI L1 Bench Electrical — Probe Sequence Checklist

*Generated: 2026-03-07T10:36:56.721395+00:00*

---

## Session 1 — Continuity Audit (Unpowered)

### 1A_GND: GND

| Pin | Symbol | Net | Type | Expected | Notes |
|-----|---|-----|---|---|---|
| 2 | VSS | GND | resistance | <=1.0 ohm | Measure resistance to chassis/reference GND |
| 4 | VSS | GND | resistance | <=1.0 ohm | Measure resistance to chassis/reference GND |
| 6 | VSS | GND | resistance | <=1.0 ohm | Measure resistance to chassis/reference GND |
| 9 | VSS | GND | resistance | <=1.0 ohm | Measure resistance to chassis/reference GND |
| 11 | VSS | GND | resistance | <=1.0 ohm | Measure resistance to chassis/reference GND |
| 13 | VSS | GND | resistance | <=1.0 ohm | Measure resistance to chassis/reference GND |
| 15 | VSS | GND | resistance | <=1.0 ohm | Measure resistance to chassis/reference GND |
| 17 | VSS | GND | resistance | <=1.0 ohm | Measure resistance to chassis/reference GND |
| 20 | VSS | GND | resistance | <=1.0 ohm | Measure resistance to chassis/reference GND |
| 22 | VSS | GND | resistance | <=1.0 ohm | Measure resistance to chassis/reference GND |
| 24 | VSS | GND | resistance | <=1.0 ohm | Measure resistance to chassis/reference GND |
| 26 | VSS | GND | resistance | <=1.0 ohm | Measure resistance to chassis/reference GND |
| 28 | VSS | GND | resistance | <=1.0 ohm | Measure resistance to chassis/reference GND |
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
| 251 | DQ45 | D5_DQ5 | continuity | PASS | Edge connector to DRAM pad (D5) |
| 253 | DQ41 | D5_DQ1 | continuity | PASS | Edge connector to DRAM pad (D5) |
| 255 | DQS5_c | D5_DQS_c | continuity | PASS | Edge connector to DRAM pad (D5) |
| 256 | DQS5_t | D5_DQS_t | continuity | PASS | Edge connector to DRAM pad (D5) |
| 258 | DQ47 | D5_DQ7 | continuity | PASS | Edge connector to DRAM pad (D5) |
| 260 | DQ43 | D5_DQ3 | continuity | PASS | Edge connector to DRAM pad (D5) |
| 262 | DQ53 | D6_DQ5 | continuity | PASS | Edge connector to DRAM pad (D6) |
| 264 | DQ49 | D6_DQ1 | continuity | PASS | Edge connector to DRAM pad (D6) |
| 266 | DQS6_c | D6_DQS_c | continuity | PASS | Edge connector to DRAM pad (D6) |
| 267 | DQS6_t | D6_DQS_t | continuity | PASS | Edge connector to DRAM pad (D6) |
| 269 | DQ55 | D6_DQ7 | continuity | PASS | Edge connector to DRAM pad (D6) |
| 271 | DQ51 | D6_DQ3 | continuity | PASS | Edge connector to DRAM pad (D6) |
| 273 | DQ61 | D7_DQ5 | continuity | PASS | Edge connector to DRAM pad (D7) |
| 275 | DQ57 | D7_DQ1 | continuity | PASS | Edge connector to DRAM pad (D7) |
| 277 | DQS7_c | D7_DQS_c | continuity | PASS | Edge connector to DRAM pad (D7) |
| 278 | DQS7_t | D7_DQS_t | continuity | PASS | Edge connector to DRAM pad (D7) |
| 280 | DQ63 | D7_DQ7 | continuity | PASS | Edge connector to DRAM pad (D7) |
| 282 | DQ59 | D7_DQ3 | continuity | PASS | Edge connector to DRAM pad (D7) |

### 1D_CA_CLK: CA CLK

| Pin | Symbol | Net | Type | Expected | Notes |
|-----|---|-----|---|---|---|
| 58 | RESET_n | RESET_n | continuity | PASS | Edge connector to bus/DRAM |
| 60 | CKE0 | CKE0 | continuity | PASS | Edge connector to bus/DRAM |
| 62 | ACT_n | ACT_n | continuity | PASS | Edge connector to bus/DRAM |
| 63 | BG0 | BG0 | continuity | PASS | Edge connector to bus/DRAM |
| 65 | A12/BC_n | A12 | continuity | PASS | Edge connector to bus/DRAM |
| 66 | A9 | A9 | continuity | PASS | Edge connector to bus/DRAM |
| 68 | A8 | A8 | continuity | PASS | Edge connector to bus/DRAM |
| 69 | A6 | A6 | continuity | PASS | Edge connector to bus/DRAM |
| 71 | A3 | A3 | continuity | PASS | Edge connector to bus/DRAM |
| 72 | A1 | A1 | continuity | PASS | Edge connector to bus/DRAM |
| 74 | CK0_t | CK_t | continuity | PASS | Edge connector to bus/DRAM |
| 75 | CK0_c | CK_c | continuity | PASS | Edge connector to bus/DRAM |
| 79 | A0 | A0 | continuity | PASS | Edge connector to bus/DRAM |
| 81 | BA0 | BA0 | continuity | PASS | Edge connector to bus/DRAM |
| 82 | RAS_n/A16 | A16 | continuity | PASS | Edge connector to bus/DRAM |
| 84 | CS0_n | CS0_n | continuity | PASS | Edge connector to bus/DRAM |
| 86 | CAS_n/A15 | A15 | continuity | PASS | Edge connector to bus/DRAM |
| 87 | ODT0 | ODT0 | continuity | PASS | Edge connector to bus/DRAM |
| 207 | BG1 | BG1 | continuity | PASS | Edge connector to bus/DRAM |
| 208 | ALERT_n | ALERT_n | continuity | PASS | Edge connector to bus/DRAM |
| 210 | A11 | A11 | continuity | PASS | Edge connector to bus/DRAM |
| 211 | A7 | A7 | continuity | PASS | Edge connector to bus/DRAM |
| 213 | A5 | A5 | continuity | PASS | Edge connector to bus/DRAM |
| 214 | A4 | A4 | continuity | PASS | Edge connector to bus/DRAM |
| 216 | A2 | A2 | continuity | PASS | Edge connector to bus/DRAM |
| 222 | PARITY | PARITY | continuity | PASS | Edge connector to bus/DRAM |
| 224 | BA1 | BA1 | continuity | PASS | Edge connector to bus/DRAM |
| 225 | A10/AP | A10 | continuity | PASS | Edge connector to bus/DRAM |
| 228 | WE_n/A14 | A14 | continuity | PASS | Edge connector to bus/DRAM |
| 232 | A13 | A13 | continuity | PASS | Edge connector to bus/DRAM |

### 1E_SPD: SPD

| Pin | Symbol | Net | Type | Expected | Notes |
|-----|---|-----|---|---|---|
| 139 | SA0 | SA0 | continuity | PASS | Edge connector to SPD EEPROM |
| 140 | SA1 | SA1 | continuity | PASS | Edge connector to SPD EEPROM |
| 141 | SCL | SPD_SCL | continuity | PASS | Edge connector to SPD EEPROM |
| 238 | SA2 | SA2 | continuity | PASS | Edge connector to SPD EEPROM |
| 285 | SDA | SPD_SDA | continuity | PASS | Edge connector to SPD EEPROM |

### 1F_NC_Isolation: NC Isolation

| Pin | Symbol | Net | Type | Expected | Notes |
|-----|---|-----|---|---|---|
| 1 | NC | NC | isolation | >=1 Mohm | Verify no short to adjacent pins |
| 8 | NC | NC | isolation | >=1 Mohm | Verify no short to adjacent pins |
| 19 | NC | NC | isolation | >=1 Mohm | Verify no short to adjacent pins |
| 30 | NC | NC | isolation | >=1 Mohm | Verify no short to adjacent pins |
| 41 | NC | NC | isolation | >=1 Mohm | Verify no short to adjacent pins |
| 47 | CB4/NC | NC | isolation | >=1 Mohm | Verify no short to adjacent pins |
| 49 | CB0/NC | NC | isolation | >=1 Mohm | Verify no short to adjacent pins |
| 51 | DM8_n/DBI8_n | NC | isolation | >=1 Mohm | Verify no short to adjacent pins |
| 52 | NC | NC | isolation | >=1 Mohm | Verify no short to adjacent pins |
| 54 | CB6/DBI8_n | NC | isolation | >=1 Mohm | Verify no short to adjacent pins |
| 56 | CB2/NC | NC | isolation | >=1 Mohm | Verify no short to adjacent pins |
| 78 | EVENT_n | NC | isolation | >=1 Mohm | Verify no short to adjacent pins |
| 89 | CS1_n | NC | isolation | >=1 Mohm | Verify no short to adjacent pins |
| 91 | ODT1 | NC | isolation | >=1 Mohm | Verify no short to adjacent pins |
| 93 | NC | NC | isolation | >=1 Mohm | Verify no short to adjacent pins |
| 100 | NC | NC | isolation | >=1 Mohm | Verify no short to adjacent pins |
| 111 | NC | NC | isolation | >=1 Mohm | Verify no short to adjacent pins |
| 122 | NC | NC | isolation | >=1 Mohm | Verify no short to adjacent pins |
| 133 | NC | NC | isolation | >=1 Mohm | Verify no short to adjacent pins |
| 144 | NC | NC | isolation | >=1 Mohm | Verify no short to adjacent pins |
| 145 | NC | NC | isolation | >=1 Mohm | Verify no short to adjacent pins |
| 192 | CB5/NC | NC | isolation | >=1 Mohm | Verify no short to adjacent pins |
| 194 | CB1/NC | NC | isolation | >=1 Mohm | Verify no short to adjacent pins |
| 196 | DQS8_c | NC | isolation | >=1 Mohm | Verify no short to adjacent pins |
| 197 | DQS8_t | NC | isolation | >=1 Mohm | Verify no short to adjacent pins |
| 199 | CB7/NC | NC | isolation | >=1 Mohm | Verify no short to adjacent pins |
| 201 | CB3/NC | NC | isolation | >=1 Mohm | Verify no short to adjacent pins |
| 203 | CKE1 | NC | isolation | >=1 Mohm | Verify no short to adjacent pins |
| 205 | NC | NC | isolation | >=1 Mohm | Verify no short to adjacent pins |
| 218 | CK1_t | NC | isolation | >=1 Mohm | Verify no short to adjacent pins |
| 219 | CK1_c | NC | isolation | >=1 Mohm | Verify no short to adjacent pins |
| 227 | NC | NC | isolation | >=1 Mohm | Verify no short to adjacent pins |
| 230 | NC | NC | isolation | >=1 Mohm | Verify no short to adjacent pins |
| 234 | NC | NC | isolation | >=1 Mohm | Verify no short to adjacent pins |
| 235 | NC | NC | isolation | >=1 Mohm | Verify no short to adjacent pins |
| 237 | NC | NC | isolation | >=1 Mohm | Verify no short to adjacent pins |

---

## Session 2 — PDN Initialization (Powered)

### 2A_Rail_Voltage: Rail Voltage

| Pin | Symbol | Net | Type | Expected | Notes |
|-----|---|-----|---|---|---|
| 59 | VDD | VDD | voltage | 1.20 V | Measure VDD rail voltage (powered, with host) |
| 142 | VPP | VPP | voltage | 2.50 V | Measure VPP rail voltage (powered, with host) |
| 284 | VDDSPD | VDDSPD | voltage | 3.30 V | Measure VDDSPD rail voltage (powered, with host) |
| 77 | VTT | VTT | voltage | 0.60 V | Measure VTT rail voltage (powered, with host) |
| 146 | VREFCA | VREF | voltage | 0.60 V | Measure VREF rail voltage (powered, with host) |

### 2B_Rail_Isolation: Rail Isolation

| Pin | Symbol | Net | Type | Expected | Notes |
|-----|---|-----|---|---|---|
| 59 | VDD(pin 59) <-> VPP(pin 142) | VDD_to_VPP | resistance | >=10 kohm | Cross-rail isolation (unpowered): VDD to VPP |
| 59 | VDD(pin 59) <-> VDDSPD(pin 284) | VDD_to_VDDSPD | resistance | >=10 kohm | Cross-rail isolation (unpowered): VDD to VDDSPD |
| 59 | VDD(pin 59) <-> VTT(pin 77) | VDD_to_VTT | resistance | >=10 kohm | Cross-rail isolation (unpowered): VDD to VTT |
| 59 | VDD(pin 59) <-> VREF(pin 146) | VDD_to_VREF | resistance | >=10 kohm | Cross-rail isolation (unpowered): VDD to VREF |
| 59 | VDD(pin 59) <-> GND(pin 2) | VDD_to_GND | resistance | >=10 kohm | Cross-rail isolation (unpowered): VDD to GND |
| 142 | VPP(pin 142) <-> VDDSPD(pin 284) | VPP_to_VDDSPD | resistance | >=10 kohm | Cross-rail isolation (unpowered): VPP to VDDSPD |
| 142 | VPP(pin 142) <-> GND(pin 2) | VPP_to_GND | resistance | >=10 kohm | Cross-rail isolation (unpowered): VPP to GND |
| 284 | VDDSPD(pin 284) <-> GND(pin 2) | VDDSPD_to_GND | resistance | >=10 kohm | Cross-rail isolation (unpowered): VDDSPD to GND |
| 77 | VTT(pin 77) <-> GND(pin 2) | VTT_to_GND | resistance | >=10 kohm | Cross-rail isolation (unpowered): VTT to GND |
| 146 | VREF(pin 146) <-> GND(pin 2) | VREF_to_GND | resistance | >=10 kohm | Cross-rail isolation (unpowered): VREF to GND |

### 2C_Power_Sequencing: Power Sequencing

| Pin | Symbol | Net | Type | Expected | Notes |
|-----|---|-----|---|---|---|
| 142 | VPP | VPP | sequencing | See notes | Must be established BEFORE VDD (JEDEC DDR4 requirement) |
| 59 | VDD | VDD | sequencing | See notes | Apply after VPP is stable |
| 284 | VDDSPD | VDDSPD | sequencing | See notes | Required for SPD EEPROM — verify present |

---

## Session 3 — SPD Bus Analysis (Powered)

### 3A_SPD_Supply: SPD Supply

| Pin | Symbol | Net | Type | Expected | Notes |
|-----|---|-----|---|---|---|
| 284 | VDDSPD | VDDSPD | voltage | 2.2-3.6 V | SPD EEPROM supply must be present before I2C read |

### 3B_I2C_Bus: I2C Bus

| Pin | Symbol | Net | Type | Expected | Notes |
|-----|---|-----|---|---|---|
| 141 | SCL | SPD_SCL | waveform | Open-drain with pull-up | Scope: verify pull-up waveform, not floating. Rise time should be consistent with I2C spec. |
| 285 | SDA | SPD_SDA | waveform | Open-drain with pull-up; ACK/NACK visible | Scope/logic analyzer: verify data transitions and ACK from EEPROM at address 0x50. |

### 3C_Address: Address

| Pin | Symbol | Net | Type | Expected | Notes |
|-----|---|-----|---|---|---|
| 139 | SA0 | SA0 | voltage | Logic LOW (tied to GND) or HIGH per design | SA pin determines EEPROM I2C address. Default 0x50 when SA0=SA1=SA2=0. |
| 140 | SA1 | SA1 | voltage | Logic LOW (tied to GND) or HIGH per design | SA pin determines EEPROM I2C address. Default 0x50 when SA0=SA1=SA2=0. |
| 238 | SA2 | SA2 | voltage | Logic LOW (tied to GND) or HIGH per design | SA pin determines EEPROM I2C address. Default 0x50 when SA0=SA1=SA2=0. |

### 3D_SPD_Read: SPD Read

| Pin | Symbol | Net | Type | Expected | Notes |
|-----|---|-----|---|---|---|
| 141 | SCL | SPD_SCL | protocol | EEPROM responds with non-0xFF/non-0x00 data | Perform I2C read at address 0x50. Verify byte 2 (SPD revision) is a valid value. All-0xFF or all-0x00 indicates blank/missing EEPROM. |

---

*Generated by generate_probe_sequence.py v1.0.0*
