The-Open-Memory-Initiative-OMI/omi/docs/08_validation_and_review/OMI Stage 8 L1 Validation Guide.md

# **Open Memory Initiative (OMI) Stage 8 Validation: Comprehensive L1 Bring-Up Playbook**

## **Executive Overview**

The Open Memory Initiative (OMI) represents a foundational paradigm shift within the open-source hardware ecosystem. By systematically deconstructing the opaque, proprietary layers historically surrounding dynamic random-access memory (DRAM) design, the initiative establishes a fully verifiable, auditable, and reproducible memory engineering pipeline.1 The overarching principle of the project dictates the elimination of undocumented "black boxes"; systems that cannot be rigorously inspected, openly peer-reviewed, and independently rebuilt cannot be trusted.2 To this end, the initiative is not pursuing commercial viability or performance supremacy, but rather structural correctness, transparency, and explainable failure modes.3

The project has successfully navigated its initial architectural phases and is currently executing Stage 8: Validation & Bring-Up Strategy.4 This critical transition phase shifts the engineering focus from theoretical computer-aided design (CAD) correctness to physical, empirical proof.5 The current v1 reference target is deliberately constrained to an 8-gigabyte, single-rank (1R), x8 unbuffered dual in-line memory module (UDIMM) running a 64-bit non-ECC bus.3

Within Stage 8, the validation methodology is strictly governed by a hierarchical "validation ladder" designed to prevent subjective or vague claims of success.5 This ladder progresses from L0 (artifact integrity) up through L4 (stress and soak testing).5 This manual is exclusively dedicated to achieving **L1**.

As explicitly defined by the primary project sources, **L1 signifies "bench electrical" validation**.4 This is the foundational physical proof that the assembled printed circuit board (PCB) operates safely and correctly *before* it is ever inserted into a host motherboard. The strict acceptance criteria for L1 encompass three domains:

1. **Continuity:** The absence of short circuits across the power delivery network (PDN) and the presence of expected routing connections.4  
2. **Rails Sane:** The ability of the module's voltage planes to accept external power without thermal runaway, excessive current draw, or voltage droop.4  
3. **SPD Bus Reads:** The reliable, noise-free extraction of configuration data from the Serial Presence Detect (EEPROM) over the physical I2C bus.4

To immediately advance the validation pipeline toward a successful L1 peer review, the assigned hardware tester must execute the following three concrete actions within the current operational week:

1. **Procure and Baseline Validation Instrumentation:** The tester must assemble, calibrate, and baseline the necessary bench-top measurement equipment. This specifically requires a current-limiting programmable DC power supply capable of independent 1.2V and 2.5V generation, a high-resolution digital multimeter (DMM) with four-wire Kelvin measurement capabilities, and an I2C-capable logic analyzer or mixed-signal oscilloscope. Establishing the baseline noise floor and transient response of this equipment is mandatory before interacting with the OMI PCB.  
2. **Execute the Unpowered Artifact Integrity Audit:** The tester must translate the frozen Stage 7 schematic netlist into a physical probing sequence. This involves executing comprehensive bare-board and assembled-board continuity checks, systematically sweeping the VPP, VDD, VDDSPD, and VREFCA domains against the VSS (Ground) plane. The output must be a densely populated, tabular impedance log proving that no manufacturing defects, solder bridges, or catastrophic layout errors compromise the fundamental isolation of the power rails.  
3. **Perform Isolated SPD Sanity Protocol Verification:** Utilizing the programmable power supply, the tester must inject an isolated 2.5V source exclusively into the VDDSPD plane, explicitly avoiding power delivery to the primary DRAM arrays. Concurrently, utilizing the logic analyzer, the tester must continuously poll the EEPROM via the I2C protocol, capturing the physical waveforms to verify precise pull-up resistor integrity, deterministic device addressing (ACK generation), and valid hexadecimal data retrieval.

## **1\. Project Posture and Current Engineering Trajectory**

The OMI operates under a strict segregation of duties, categorizing contributors into Developers (tooling and automation), Reviewers (correctness and internal consistency), and Testers (hardware bring-up and physical evidence generation).2 To execute L1 effectively, a Tester must fundamentally understand the upstream decisions that constrain the physical hardware under test.

The following table synthesizes the exact current state of the initiative, establishing the frozen parameters, the active Stage 8 mandates, and the future trajectory. This serves as the operational baseline for all subsequent physical testing.

| Project State Parameter | Context and Engineering Implication | Authoritative Source |
| :---- | :---- | :---- |
| **Philosophical Mandate** | The project rejects undocumented specification dumps and vendor-gated simulation models. Every claim requires explicit assumptions, structured review, and reproducible physical evidence. Testers must not rely on proprietary JEDEC materials if they cannot be publicly cross-referenced. | 2 |
| **V1 Target Architecture Lock** | The hardware is strictly defined as a DDR4 UDIMM, 8GB capacity, Single Rank (1R), utilizing x8 DRAM ICs. Dual-rank, ECC, and advanced topologies (LPDDR/HBM) are explicitly out of scope, simplifying the necessary L1 routing complexity and current draw expectations. | 3 |
| **Stage 5 Status: Frozen** | The baseline architecture decisions regarding the DDR4 implementation are finalized. No further fundamental logic changes will be accepted. | 3 |
| **Stage 6 Status: Frozen** | The logical block decomposition is locked. The design is compartmentalized into discrete Power/PDN, Command/Address/Clock (CA/CLK), Data (DQ/DQS), and SPD blocks. L1 troubleshooting must respect these operational boundaries. | 3 |
| **Stage 7 Status: Frozen** | Schematic capture is complete. The electrical intent, including star-routing topologies for CA/CLK and edge pin map integrity across all 288 pins, represents the definitive truth for unpowered continuity checking. | 4 |
| **Stage 8 Status: Active** | The project has entered "Validation & Bring-Up Strategy." The engineering focus has shifted from CAD theory to creating the procedures, checklists, and failure catalogs necessary to prove the schematic functions in reality. | 5 |
| **Validation Ladder Framework** | To combat subjective claims ("it works on my machine"), Stage 8 introduces a non-negotiable ladder: L0 (Artifacts), L1 (Bench), L2 (Host), L3 (Boot), L4 (Stress). Progression is strictly sequential; skipping steps invalidates the review. | 5 |
| **L1 Definition Lock** | L1 is explicitly defined as physical bench electrical verification, comprising continuity checks, power rail sanity, and SPD I2C reads prior to motherboard insertion. | 4 |
| **Host System Exclusion (L1)** | Inserting the module into a host BIOS environment is strictly prohibited during L1. The host environment introduces confounding variables (BIOS logic, memory controller training) that obscure fundamental electrical faults. | 6 |
| **Reviewer Independence** | The engineer executing the L1 bench tests cannot self-certify the results. A Track 02 Reviewer must audit the submitted evidence packages (logs, traces) against the established rubrics before the module advances to L2. | 2 |
| **Failure Documentation Mandate** | The OMI requires failures to be published alongside successes. Identifying and documenting "rookie-killer" mistakes, topology constraints, and PDN realities is a primary objective of Stage 8, not an ancillary task. | 4 |
| **Exclusion of Vendor "Black Boxes"** | Simulation inputs or IBIS models that are restricted by NDA or require corporate lab resources are excluded from the critical path. Validation relies purely on empirical bench data derived from open instrumentation. | 3 |
| **Future Stage 9 Scope** | Upon validation strategy finalization, Stage 9 will generate the minimal reference schematic, representing a single-rank, unoptimized baseline design. | 4 |
| **Future Stage 10 Scope** | Stage 10 will establish the physical layout constraints, dictating Signal Integrity and Power Integrity (SI/PI) rules, trace impedance targets, and standard routing patterns. | 4 |
| **Tooling and CI Automation** | Track 01 Developers are actively building linters, consistency checkers, and reporting templates via GitHub Actions to automate the verification of L0 and the formatting of L1/L2 data submissions. | 2 |

## **2\. Stage 8 Document Hierarchy and Architectural Map**

Stage 8 operates as a highly structured bureaucratic mechanism ensuring that physical validation translates back into public, verifiable data. The core repository directory intended to house these artifacts is docs/08\_validation\_and\_review/.9

Uncertainty Declaration: During the synthesis of this report, direct programmatic crawling of the internal GitHub blobs within docs/08\_validation\_and\_review/ returned HTTP accessibility errors (likely due to temporary repository configuration states, rate limits, or branch transitions).10 However, the strict hierarchical requirements of Stage 8 are extensively documented across the author's public engineering syndications.4 The following map is a high-confidence, deduced reconstruction of the required documentation structure based on the explicit project mandates.

*Verification Method: To verify this structure, the testing engineer must clone the primary OMI repository locally (git clone https://github.com/The-Open-Memory-Initiative-OMI/omi.git), checkout the main branch, and execute tree docs/08\_validation\_and\_review via the command line interface to cross-reference the presence and naming conventions of the files listed below.*

| Directory / File Path | Purpose and Rationale | Operational Usage Context | Expected Output Artifact |
| :---- | :---- | :---- | :---- |
| docs/08\_validation\_and\_review/README.md | Establishes the foundational philosophy of Stage 8, detailing the L0-L4 validation ladder and explicitly forbidding reliance on undocumented simulation inputs. | Read thoroughly prior to any hardware interaction to calibrate the tester's engineering mindset toward evidence-based reporting. | N/A (Normative Guidance) |
| docs/08\_validation\_and\_review/00\_platform\_selection.md | Dictates the constraints for selecting consumer-grade host hardware (motherboards, CPUs, BIOS versions) intended to minimize platform-induced variance. | Utilized to requisition and baseline the specific host test bench required for subsequent L2 and L3 testing phases. | A hardware manifest documenting the authorized motherboard and processor stepping. |
| docs/08\_validation\_and\_review/01\_L1\_bench\_electrical.md | Contains the definitive, sequential unpowered and powered bench safety checks required immediately upon receiving the fabricated PCBs. | Executed physically on the test bench to identify fundamental manufacturing defects or gross assembly errors. | A populated L1 validation report, complete with resistance logs and oscilloscope exports. |
| docs/08\_validation\_and\_review/02\_bring\_up\_procedure.md | Details the sequential progression from L2 (Host Enumeration) through L4 (Stress and Soak), covering BIOS interaction, training algorithms, and OS-level testing. | Referenced sequentially only after L1 is formally signed off and peer-reviewed by a Track 02 contributor. | A comprehensive bring-up log indicating precise points of BIOS or training failure. |
| docs/08\_validation\_and\_review/03\_failure\_mode\_catalog.md | A living document aggregating known "rookie-killer" errors, PDN inadequacies, thermal events, and topology collapse scenarios observed during testing. | Consulted during active diagnostic troubleshooting when empirical hardware behavior deviates from schematic expectations. | Detailed root-cause analysis reports mapped to specific hardware anomalies. |
| docs/08\_validation\_and\_review/templates/L1\_report\_template.md | Provides a rigid, structured Markdown format to ensure uniformity of evidence submission across disparate global hardware testers. | Duplicated and populated during the conclusion of the testing phase to prevent unstructured, anecdotal claims of functionality. | A standardized Pull Request (PR) containing the raw validation evidence files. |
| docs/08\_validation\_and\_review/templates/review\_checklist.md | Serves as the grading rubric for Track 02 Reviewers assigned to audit a tester's L1, L2, or L3 PR submission. | Utilized asynchronously by a secondary engineer to systematically verify the primary tester's logic traces and electrical logs. | A formal PR approval, or a documented, specific request for re-testing and data correction. |

## **3\. Precise Definition and Criteria for L1 Success**

In the realm of open-source hardware, the assertion that a complex high-speed design "works" is frequently plagued by subjective bias and inadequate testing conditions. The OMI completely eradicates this ambiguity through the rigid implementation of the Validation Ladder.

L1—Bench Electrical—represents the absolute foundational layer of empirical reality. It is predicated on the engineering reality that inserting an untested DDR4 UDIMM directly into a high-performance motherboard is hazardous; the motherboard's power management ICs (PMICs), complex memory controller training algorithms, and obscure BIOS logic create a highly obfuscated environment. A failure at the BIOS level provides virtually no diagnostic insight into whether the failure is a software incompatibility or a physical dead-short on a secondary power plane.4

The OMI explicitly defines L1 success through three isolated, verifiable criteria: **continuity**, **rails sane**, and **SPD bus reads**.4

### **A. The Definitive L1 Pass/Fail Checklist**

To achieve a verified L1 state, the hardware must independently pass the following rigorous checks using external bench instrumentation, completely isolated from a host motherboard.

**Domain 1: Continuity and Short-Circuit Clearance (Unpowered State)**

The primary objective is to prove the PCB fabrication and the surface-mount technology (SMT) assembly process did not introduce fatal cross-plane shorts or open circuits.

* \[ \] The primary 1.2V core logic plane (VDD) exhibits an appropriate, high-ohmic impedance path to the Ground plane (VSS), strictly indicating typical decoupling capacitor leakage rather than a metallic short.  
* \[ \] The 2.5V wordline activation plane (VPP) exhibits high-ohmic isolation from the VSS plane.  
* \[ \] The 2.5V EEPROM power plane (VDDSPD) exhibits high-ohmic isolation from the VSS plane.  
* \[ \] The command/address reference plane (VREFCA) exhibits correct isolation from both VDD and VSS.  
* \[ \] The I2C Data (SDA) and Clock (SCL) signal lines exhibit the precise mathematically expected pull-up resistance relative to the VDDSPD plane (typically 2.2kΩ to 4.7kΩ).  
* \[ \] All 288 edge connector pads are visually and electrically confirmed to be free of solder bridging or masking errors.

**Domain 2: Power Delivery Network (PDN) Sanity (Externally Powered State)**

The objective is to prove the module's planar copper layout can accept steady-state power without parasitic oscillation, excessive resistance causing voltage droop, or localized thermal runaways.

* \[ \] Upon external injection via a current-limited supply, the VPP rail maintains a highly stable 2.5V (±5% tolerance) under steady-state quiescent conditions without triggering over-current protection.  
* \[ \] The VDD rail maintains a highly stable 1.2V (±5% tolerance) under steady-state quiescent conditions, drawing a current strictly aligned with the standby leakage characteristics of eight x8 DDR4 ICs.  
* \[ \] The VDDSPD rail maintains a stable 2.5V.  
* \[ \] Under continuous power application (minimum 15-minute soak), comprehensive thermal observation utilizing an infrared camera reveals no surface-mount component (capacitor, resistor, or IC package) exceeding ambient room temperature by more than a 15°C delta.

**Domain 3: Serial Presence Detect (SPD) Integrity (Isolated Active State)**

The objective is to verify that the digital management interface operates perfectly at the physical layer, ensuring the motherboard will be able to interrogate the module later in L2.

* \[ \] Injecting 2.5V exclusively into the VDDSPD plane powers the SPD EEPROM independently, without causing parasitic voltage leakage into the VDD or VPP planes through clamping diodes.  
* \[ \] A logic analyzer, acting as an I2C master device, transmits a query sequence on the SDA/SCL lines and receives a crisp, valid low-voltage acknowledgment (ACK) bit from the module at the expected hexadecimal address. (The specific address, typically 0x50 through 0x57, is dictated by the hardwired state of the edge connector's SA0, SA1, and SA2 address strapping pins).  
* \[ \] A contiguous memory dump of the initial 64 bytes of the SPD EEPROM yields valid, structured data arrays corresponding to JEDEC configuration parameters, rather than returning bus contention noise or continuous 0xFF outputs.

### **B. Required Evidence Artifacts**

Under the Track 02 reviewer mandate, anecdotal tester claims are inadmissible.2 To pass L1, the following highly specific digital artifacts must be captured, cataloged, and committed to the public repository alongside the PR:

* **Artifact 1: The Impedance Matrix Log.** A highly structured .csv file or Markdown table documenting the exact Ohmic resistance measured between every major power rail and the VSS plane. This document proves the absence of localized shorts and validates the presence of expected decoupling capacitance.  
* **Artifact 2: Power Sequencing Oscilloscope Capture.** A high-resolution image (.png) or raw data export (.csv) from a digital storage oscilloscope (DSO) illustrating the simultaneous turn-on behavior of the VPP and VDD planes injected via the edge connector. The trace must definitively prove that the planes charge smoothly without severe high-frequency ringing, under-damped oscillations, or voltage droops indicative of severe planar inductance.  
* **Artifact 3: I2C Logic Analyzer Trace Extraction.** A raw binary dump file (e.g., a Sigrok .sr file) paired with a visual software screenshot (from PulseView or Saleae Logic). The trace must possess sufficient sample rate (minimum 10 MS/s) to clearly resolve the analog rise time of the I2C bus, the START condition, the 7-bit device address, the precise 9th clock pulse ACK bit, and a minimum of one successful byte read operation.

### **C. Common Failure Modes and Diagnostic Protocols**

When physical reality diverges from the schematic intent, systematic diagnostic protocols are required.4

* **Failure Mode Identifier:** A near-zero Ohm measurement (e.g., 0.2Ω) between the primary VDD plane and VSS.  
  * *Diagnostic Action:* Do not apply power. This is a catastrophic hard short. Utilize a high-magnification stereomicroscope to cross-check the densest clusters of 0402 or 0201 surface-mount decoupling capacitors surrounding the BGA footprints. Solder paste bridging under the capacitors is the primary culprit. Sequentially desolder and remove capacitors starting from the most congested routing areas until the impedance matrix clears to a high-ohmic state.  
* **Failure Mode Identifier:** The SPD EEPROM fails to acknowledge (NACK) the transmitted I2C address query.  
  * *Diagnostic Action:* Verify the logic state of the SA0, SA1, and SA2 address strapping pins located on the edge connector. In a standard host environment, the motherboard pulls these pins to defined states. On an isolated test bench, they may be floating, causing the EEPROM's internal logic to interpret random noise as an address change. Force the pins to VSS temporarily. Furthermore, utilize a DMM to measure the physical DC voltage at the SDA/SCL pull-up resistors; if they do not register at approximately 2.5V, the pull-ups are absent, improperly populated, or the VDDSPD planar trace is severed.  
* **Failure Mode Identifier:** The VDD rail exhibits severe, continuous voltage ripple when powered by the bench supply.  
  * *Diagnostic Action:* This indicates either a fundamental failure of the module's bulk decoupling strategy or, more commonly, severe inductive loops created by excessively long, untwisted test leads connecting the power supply to the module. Shorten the bench supply cables drastically, twist the positive and negative leads together to minimize loop inductance, and retest. If the ripple persists under nominal DC load, the localized PDN on the PCB is intrinsically inadequate.

### **D. Suggested Standard Augmentation (Addressing Underspecified Criteria)**

Because the precise normative content of the 01\_L1\_bench\_electrical.md criteria document is currently gated by access restrictions, the public definition leaves a minor gap between L0 (artifact consistency) and L1 (bench electrical).11

* *Suggested Augmentation:* To create a fully credible L1 standard consistent with the repository's philosophical intent, the protocol must mandate **Pin-Mapping Continuity Verification**.  
* *Rationale:* Simply measuring power planes does not guarantee that the high-speed data lines physically routed correctly from the edge connector to the DRAM BGA pads. A fabrication error could sever traces.  
* *Execution:* The tester must select a minimum of five random data pins (e.g., DQ14, DQ22, DQ41, DQ55, DQ61) at the 288-pin edge connector. Utilizing a DMM equipped with fine-point needle probes, measure the resistance between the edge connector pad and the corresponding physical via located adjacent to the target DRAM chip. The resistance must read less than 1.0 Ohm. This physically proves that the Stage 7 schematic netlist successfully translated into continuous copper routing during CAM processing and PCB manufacturing.

## **4\. Targeted Learning Plan: Engineering Prerequisites for L1**

Achieving L1 requires a highly specific subset of hardware engineering skills. It is crucial to note that L1 explicitly does *not* require advanced knowledge of high-speed Signal Integrity (SI), S-parameter modeling, impedance matching, or memory controller training algorithms.3 Those competencies are strictly reserved for L3 and L10.4 The learning plan required for L1 is restricted entirely to fundamental bench electrical disciplines and low-speed protocol analysis.

### **A. Foundational Prerequisites (Concepts to Master First)**

* **Topic: JEDEC DDR4 Power Architecture Fundamentals.**  
  * *Concept:* The engineer must understand the distinct, isolated roles of the various power rails entering the DDR4 UDIMM. VDD (1.2V) supplies the primary core logic and I/O buffers of the DRAM. VPP (2.5V) is exclusively utilized for the internal wordline activation pumps within the DRAM silicon, heavily reducing the power burden on the 1.2V plane. VDDSPD (2.5V) isolates the EEPROM power from the electrically noisy main memory arrays. VREFCA (0.6V) provides the analog reference threshold for interpreting command and address signals.  
  * *Verification:* The engineer must be capable of drawing a rudimentary block diagram illustrating these four rails and their independent paths to ground without referencing documentation.  
* **Topic: Four-Wire (Kelvin) Resistance Measurement Theory.**  
  * *Concept:* Understanding why a standard, two-wire digital multimeter measurement is intrinsically flawed when detecting milliohm-level shorts on thick-copper PCBs. The internal resistance of the test leads and the contact resistance of the probes frequently exceed the resistance of the short circuit itself. Kelvin sensing uses four wires (two for sourcing a constant test current, two for highly sensitive voltage measurement) to completely eliminate lead resistance from the calculation.  
  * *Verification:* The engineer must be able to accurately measure a known 0.1-ohm shunt resistor using a DMM and obtain a reading accurate to within 5% of the nominal value.  
* **Topic: I2C Digital Protocol Mechanics.**  
  * *Concept:* Understanding the physics of open-drain topologies. In I2C, devices only actively pull the signal line down to ground (logic 0); they rely entirely on external pull-up resistors to return the line to the high voltage state (logic 1). The engineer must grasp how the RC time constant (determined by the pull-up resistor value and the parasitic capacitance of the bus) dictates the rise time and maximum operational frequency of the bus.  
  * *Verification:* The engineer must be able to visually identify a "NACK" (where the line floats high during the 9th clock pulse) versus bus contention (where the voltage hangs ambiguously between high and low thresholds) on an oscilloscope screen.

### **B. Core OMI-Specific Topics**

* **Topic: Physical Pinout Mapping and Translation.**  
  * *Read in Repo:* Review the comprehensive schematic PDF generated during Stage 7\.4 Locate the massive 288-pin edge connector symbol and trace the specific clusters representing the VDD and VSS pins.  
  * *Practice Exercise:* Print a highly magnified physical layout of the DDR4 edge connector gold fingers. Utilizing colored markers, manually highlight the VDDSPD pin (physically located at Pin 255 on a standard DDR4 UDIMM), the SDA pin, and the SCL pin.  
  * *Verification:* The engineer should possess the spatial awareness to blindly locate the SPD communication interface on a blank, physical PCB using solely visual inspection of the alignment notch and the gold fingers.  
* **Topic: PDN Isolation and Leakage Calculations.**  
  * *Read in Repo:* Review the Stage 6 block decomposition documentation, focusing explicitly on the Power/PDN block architectural intent.4  
  * *Practice Exercise:* Identify the total count of decoupling capacitors on the VDD plane. Calculate the expected parallel resistance based on the cumulative DC leakage currents specified in standard ceramic capacitor datasheets.  
  * *Verification:* The engineer must be equipped to state a hard, numerical threshold prior to testing (e.g., "Given the component count, any resistance measured below 15 Ohms on the VDD plane constitutes a hard short and an immediate failure condition").

### **C. Tools and Operational Workflows**

* **Workflow: KiCad Cross-Probing Dynamics.**  
  * *Action:* Install KiCad and load the native OMI v1 PCB layout file. Master the cross-probing interface: learn to click a logical net in the schematic (e.g., VDD\_1V2) and observe the software instantly highlight every corresponding physical trace, via, and copper pour across all physical layers of the board. This specific software workflow is absolutely critical for knowing exactly where to place multimeter needle probes during the physical continuity testing phase.  
* **Workflow: Logic Analyzer Triggering and Decoding.**  
  * *Action:* Install the open-source PulseView logic analysis suite. Connect a USB logic analyzer to a known-good, independent I2C device (such as an Arduino environmental sensor breakout board). Practice configuring the software to trigger specifically on the falling edge of the SDA line (the standard I2C START condition) and applying the protocol decoder to translate the waveforms into hexadecimal text. This ensures the instrumentation is calibrated before introducing the complexity of the OMI hardware.  
* **Workflow: Current-Limited Power Supply Discipline.**  
  * *Action:* Master the interface of the programmable bench DC power supply. Specifically, learn to set strict Over-Current Protection (OCP) limits. For L1 testing, setting a hard constant-current limit of 100mA ensures that if a dead short is present on the PCB, the power supply will instantly collapse the voltage rather than pumping massive current into the board, thereby preventing the catastrophic vaporization of delicate copper traces.

## **5\. Step-by-Step Execution Guide to Achieve L1**

This section constitutes the primary operational deliverable of this playbook. It is divided into three highly structured, sequential sessions designed to be executed in discrete 30 to 90-minute intervals.

**Mandatory Rule:** The engineer must strictly obey the defined STOP/GO gates. Proceeding to a subsequent session while a previous gate indicates a failure will inevitably result in hardware destruction or invalid data artifacts.

### **Session 1: Pre-Power Artifact and Continuity Audit**

**Time Allocation:** 45 Minutes

**Goal:** Prove conclusively that the manufactured PCB exactly mirrors the frozen Stage 7 schematic intent, and verify the total absence of catastrophic short circuits prior to any energy introduction.

**Exact Actions:**

1. Launch the KiCad layout file containing the OMI v1 design. Utilize the net inspector to explicitly highlight the entire GND (VSS) reference net across all layers.  
2. Configure the bench Digital Multimeter (DMM) to high-precision resistance (Ohms) mode. Do *not* use the audible continuity "beep" mode for final logging, as it provides insufficient granularity.  
3. Securely place the negative (black) test probe onto a known, highly accessible VSS gold finger on the edge connector (e.g., Pin 4 or Pin 13).  
4. Systematically and carefully probe the following power input pins on the edge connector, applying light pressure to avoid scratching the gold plating:  
   * Primary Core Logic: VDD (1.2V) \- e.g., Pin 17  
   * Wordline Pump: VPP (2.5V) \- e.g., Pin 18  
   * EEPROM Power: VDDSPD (2.5V) \- Pin 255  
   * Analog Reference: VREFCA \- Pin 167  
5. Allow the DMM reading to stabilize (the initial reading will climb as the module's bulk capacitance charges from the DMM's internal test voltage). Record the stabilized Ohmic values into a blank spreadsheet.

**Expected Outputs:** The multimeter display should register infinite resistance (over-limit/OL) or values deep into the high-megohm range. A brief, transiently low resistance that climbs rapidly is the expected physical behavior of charging capacitors. A static, non-climbing resistance below 50 ohms is a failure.

**Verification Method:** Cross-reference the empirical DMM readouts against the theoretical expected parallel resistance of the unpowered integrated circuits.

**Evidence to Capture:** Export the spreadsheet as a .csv file detailing the specific resistance of every major power net relative to the Ground plane. Save this file to the local repository clone under docs/08\_validation\_and\_review/evidence/YOUR\_NAME/session1\_continuity.csv.

**STOP/GO Gate:** If any primary rail (VDD, VPP, VDDSPD) measures a static resistance below 10 Ohms to ground, **STOP IMMEDIATELY**. Do not proceed to Session 2\. Inspect the board under magnification for SMT solder bridges. If all major rails exhibit appropriately high impedance, **GO**.

### **Session 2: Low-Voltage PDN Initialization and Thermal Audit**

**Time Allocation:** 60 Minutes

**Goal:** Prove the primary power planes can safely accept voltage initialization without drawing anomalous parasitic current, triggering constant-current limits, or exhibiting localized thermal runaway.

**Exact Actions:**

1. Configure the dual-channel programmable bench power supply prior to connection: Set Channel 1 to 2.5V with a strict current limit of 50mA. Set Channel 2 to 1.2V with a strict current limit of 100mA. Disable both outputs.  
2. *Crucial DDR4 Electrical Constraint:* Power sequencing logic dictates that VPP (2.5V) must be fully established before VDD (1.2V) begins to rise to prevent internal silicon latch-up.  
3. Carefully solder temporary, fine-gauge (e.g., 30 AWG) test-point wires to accessible vias or test pads connected to the VPP, VDD, and VSS planes on the module. Connect these wires to the power supply leads.  
4. Activate Channel 1 (2.5V to VPP). Immediately observe the current draw displayed on the bench supply screen.  
5. Wait two seconds. Activate Channel 2 (1.2V to VDD). Immediately observe the current draw.  
6. Utilize a high-resolution thermal imaging camera (or, lacking one, carefully apply high-purity isopropyl alcohol and monitor evaporation rates) to sweep the entire PCB, scrutinizing the DRAM packages and dense decoupling capacitor clusters for localized hot spots.

**Expected Outputs:** The steady-state current draw on the VPP plane should be virtually negligible (typically under 5mA). The current draw on the VDD plane should align strictly with the baseline standby leakage of eight uninitialized x8 DDR4 ICs (typically summing to 20-40mA total). The thermal sweep should reveal absolutely no component exceeding the ambient room temperature.

**Verification Method:** Visual confirmation of the digital current readouts on the power supply interface and thermal uniformity across the PCB surface.

**Evidence to Capture:** Capture a high-resolution, wide-angle photograph of the test bench clearly showing the active power supply screen displaying the steady-state voltages and current draws while physically connected to the module. Save as docs/08\_validation\_and\_review/evidence/YOUR\_NAME/session2\_power\_steady\_state.jpg.

**STOP/GO Gate:** If the power supply instantly hits the constant-current (CC) threshold and collapses the voltage, **STOP**. A high-resistance short or reversed diode is present on the rail. If the voltages hold absolutely steady at 2.5V and 1.2V with nominal current leakage, **GO**.

### **Session 3: SPD Bus Initialization and Logic Analysis**

**Time Allocation:** 90 Minutes

**Goal:** Verify foundational digital communication capabilities by successfully reading the configuration EEPROM over the I2C bus, establishing that the management interface is fully operational prior to host BIOS insertion.

**Exact Actions:**

1. Completely disable Channel 1 and Channel 2 on the power supply. Ensure the module is fully unpowered and discharged.  
2. Reconfigure the bench supply to 2.5V, with a highly restrictive current limit of 20mA. Connect this source exclusively to the VDDSPD pad and VSS. Activate the power output.  
3. Connect the ground reference lead of the logic analyzer directly to the module's VSS plane to ensure a common reference potential.  
4. Connect logic analyzer Channel 0 to the SDA (Serial Data) edge pin and Channel 1 to the SCL (Serial Clock) edge pin using micro-grabbers.  
5. Launch the PulseView software environment. Add the I2C protocol decoder to the workspace. Configure the sampling rate to a minimum of 10 MS/s to ensure adequate resolution of the analog signal transitions.  
6. Utilize a secondary, independent microcontroller (e.g., an Arduino Uno or Raspberry Pi Pico) pre-programmed with a basic I2C bus scanner script. Connect its SDA and SCL output lines to the corresponding pins on the module. Ensure the microcontroller is utilizing 2.5V or 3.3V logic levels (5V logic will destroy the EEPROM).  
7. Configure PulseView to trigger on the falling edge of Channel 0 (SDA), which represents the mandatory I2C START condition. Arm the trigger.  
8. Execute the I2C scan routine from the external microcontroller.

**Expected Outputs:** The logic analyzer will capture a clean START condition. The microcontroller will sequentially transmit 7-bit addresses. When it transmits the specific address strapped to the EEPROM (e.g., 0x50), the module's EEPROM will actively pull the SDA line low during the 9th clock pulse, signifying a valid hardware ACK.

**Verification Method:** The PulseView protocol decoder engine successfully translates the captured waveforms into hexadecimal text blocks without flagging framing errors, missing ACKs, or timing violations.

**Evidence to Capture:** Export the graphical logic analyzer trace clearly highlighting the successful ACK bit. Save as session3\_spd\_ack\_trace.png. Additionally, export the raw timing data as session3\_raw\_capture.sr. Save both to the evidence directory.

**STOP/GO Gate:** If the SDA line remains pegged high (indicating a NACK) or never reaches the 2.5V threshold (indicating a missing or failed pull-up resistor), **STOP**. Systematically troubleshoot the physical addressing pins (SA0-SA2) and verify pull-up resistor continuity. If a solid ACK is received and hex byte data is readable, **GO**.

**Achievement Unlocked:** The hardware has successfully satisfied all rigorous L1 requirements. It is now electrically verified, proven safe, and cleared for insertion into a live host motherboard for L2 (Host Enumeration) phase testing.

## **6\. Deliverable PR Templates**

To guarantee strict compliance with the OMI evidence-based philosophy and to streamline the Track 02 review process, testers must utilize the following highly structured Markdown templates to construct their final Pull Request submission.2

### **A. L1 Report Template (To be filled by the Tester)**

# **L1 Bench Electrical Validation Report**

**Testing Engineer:** \[Name/GitHub Handle\]

**Date of Test Execution:**

**Hardware Revision Under Test:** OMI v1.0 (DDR4 UDIMM 8GB 1R x8)

**PCB Manufacturer / SMT Assembly:**

## **1\. Executive Summary**

The physical module was subjected to the mandatory L1 validation ladder protocols, encompassing unpowered continuity verification, powered PDN stability analysis, and isolated SPD digital communication checks.

**Final L1 Status:**

## **2\. Rigorous Acceptance Criteria Checklist**

* \[ \] Primary VDD plane is electrically isolated from VSS (Measured impedance: \[XX.X\] K-Ohms)  
* \[ \] Secondary VPP plane is electrically isolated from VSS (Measured impedance: \[XX.X\] M-Ohms)  
* \[ \] VDDSPD plane is electrically isolated from VSS (Measured impedance: \[XX.X\] M-Ohms)  
* \[ \] Steady-state quiescent power draw remains within theoretical limits (VDD: \[XX\] mA, VPP: \[XX\] mA)  
* \[ \] Thermal audit confirms no localized heating above ambient \+ 15°C  
* \[ \] Logic analyzer confirms SPD EEPROM acknowledges external I2C master at address \[0xXX\]

## **3\. Mandatory Evidence Artifacts**

*All referenced files are committed within /docs/08\_validation\_and\_review/evidence/\[NAME\]/*

* **Impedance Matrix Log:** \[Insert relative link to session1\_continuity.csv\]  
* **Power Supply Telemetry Capture:** \[Insert relative link to session2\_power\_steady\_state.jpg\]  
* **Logic Analyzer Protocol Trace:** \[Insert relative link to session3\_spd\_ack\_trace.png\]

## **4\. Methodological Deviations and Physical Observations**

*Document any deviations from the standard playbook or physical rework performed. Example: "Initially failed VDD continuity check due to a microscopic solder bridge at C42. Manually reflowed the component using hot air, which successfully cleared the 12-ohm leak, returning the plane to high-impedance."*

## **5\. Re-Test Notes (If Applicable)**

*If this PR represents a subsequent attempt following a previous Track 02 rejection, detail exactly what structural variables were modified to correct the previously observed failure mode.*

### **B. Review Checklist Template (To be filled by the Track 02 Reviewer)**

# **L1 Peer Review Audit Rubric**

**Reviewing Engineer:** \[Name/GitHub Handle\]

**Target Pull Request:** \#

## **Validation Ladder L1 Rubric Evaluation**

* \[ \] **Artifact Integrity & Plausibility:** The submitted CSV impedance log includes discrete measurements for all critical nets. The recorded resistance values represent plausible physical realities (e.g., measurements are not perfectly infinite, nor absolute zero, but reflect the expected charging curves of the planar decoupling capacitors).  
* \[ \] **Photographic Evidence Verification:** The submitted power supply imagery clearly displays the stated voltage limits and demonstrates steady-state current constraints without visual ambiguity or cropping.  
* \[ \] **Digital Trace Sanity:** The logic analyzer trace explicitly identifies a valid, low-voltage ACK bit. The physical analog waveform characteristics (rise time, fall time) do not indicate excessive bus contention, improper RC time constants, or poor ground referencing.  
* \[ \] **Methodological Rigor:** The testing engineer sufficiently documented the ambient environmental conditions and the exact make/model of the bench instrumentation utilized (e.g., Rigol DP832 PSU, Saleae Logic 8 Analyzer), establishing full repeatability.

**Final Review Decision:**

**Justification and Engineering Feedback:**

### **C. Public Issue/PR Update Format**

**Status Update: L1 Validation Successfully Concluded**

The Stage 8 L1 (Bench Electrical) procedures have been fully executed on the v1 physical reference design.

**Core Engineering Findings:**

* PDN continuity is solid; the multi-layer bulk decoupling strategy is holding charge without detecting leakage paths.  
* Mandatory power sequencing logic (VPP scaling prior to VDD introduction) executes cleanly on the bench without triggering anomalous current spikes.  
* The SPD management bus responds correctly to external I2C masters at address 0x50.

**Artifacts Attached:** The formal L1 Report Markdown, Logic analyzer traces (.sr and .png), and DMM impedance exports are included in the PR commit history.

**Next Steps:** The package is currently awaiting Track 02 peer review. Assuming clearance, physical testing will transition to the L2 (Host Enumeration) protocol utilizing the authorized \[Insert Motherboard Model\] test bench structure.

## **7\. L1 Risk Register ("Rookie-Killer" Failure Modes)**

The OMI repository explicitly mandates the aggregation and cataloging of "rookie-killer" module pitfalls—mistakes that cause a design to appear plausible in CAD software but inevitably collapse under the physical variance of the real world.3 During L1 bring-up, specific anti-patterns yield hardware that "seems to work" to an untrained eye but fundamentally fails rigorous electrical safety checks.4 This risk register serves to aggressively mitigate these exact testing traps.

**1\. The Floating SPD Address Pin Oscillation**

* **Symptom:** The logic analyzer captures a perfectly formed I2C START condition and an impeccably timed address query, yet the SPD EEPROM continuously returns a NACK (the SDA line remains high).  
* **Likely Root Cause:** The schematic relies entirely on the host motherboard to pull the SA0, SA1, and SA2 address pins into defined high or low states. On an isolated test bench, outside the motherboard slot, these pins float. High-impedance CMOS logic inputs interpret floating pins randomly based on ambient electromagnetic noise, causing the EEPROM's internal logic to adopt a rapidly shifting, indeterminate I2C address.  
* **How to Catch it Early:** Review the schematic thoroughly during the L0 artifact phase. Ensure the bench test setup includes the temporary application of 10kΩ pull-down or pull-up resistors on the address pins to force a deterministic state (e.g., tying all three pins to VSS to definitively force the address to 0x50).  
* **Evidence Proving it is Fixed:** A logic analyzer trace showing a solid, sustained ACK specifically at the hardwired address, remaining stable across multiple query attempts.

**2\. I2C Bus Loading and Signal Degradation via Instrument Probes**

* **Symptom:** SPD communication functions perfectly when only the logic analyzer is connected, but immediately fails or generates corrupted, garbage hex data when a multimeter or oscilloscope is simultaneously probing the active SDA data line.  
* **Likely Root Cause:** The combined parasitic capacitance of the logic analyzer probes, the oscilloscope probes, and the test leads greatly exceeds the drive capability of the relatively weak I2C pull-up resistors (often selected at 2.2kΩ or 4.7kΩ to save power). Because I2C is an open-drain protocol, this massive RC time constant slows the rise time of the signal significantly. The voltage simply cannot rise fast enough to register as a valid logic '1' threshold before the next clock pulse initiates.  
* **How to Catch it Early:** Enforce strict instrumentation discipline. Never probe active, open-drain digital buses with multiple high-capacitance instruments simultaneously during active data transmission.  
* **Evidence Proving it is Fixed:** An oscilloscope capture of the SDA and SCL lines demonstrating crisp, highly vertical square waves with rise times remaining well under the JEDEC maximum threshold (typically under 1000 nanoseconds) when driven solely by the onboard pull-up architecture.

**3\. Ignoring JEDEC VPP to VDD Power Sequencing Dictates**

* **Symptom:** L1 powered tests exhibit highly erratic current draw on the primary VDD plane, or the DRAM IC packages become physically warm even when absolutely no clock signals or data strobes are present on the bus.  
* **Likely Root Cause:** The JEDEC DDR4 electrical standards strictly require the 2.5V VPP rail to be established *before* the 1.2V VDD rail. Applying VDD first can inadvertently forward-bias internal electrostatic discharge (ESD) protection diodes or induce parasitic thyristor latch-up within the complex CMOS silicon structure of the DRAM. This causes the chip to draw massive, unregulated current, permanently degrading the component.  
* **How to Catch it Early:** Incorporate delayed-start relays into the test rig, or strictly utilize a programmable power supply with absolute, programmable power-sequencing capabilities during Session 2\.  
* **Evidence Proving it is Fixed:** A dual-channel oscilloscope trace explicitly demonstrating the VPP rail rising smoothly and stabilizing fully at 2.5V a minimum of 2 milliseconds prior to the VDD rail lifting above the 0V threshold.

**4\. The "Looks Connected" CAD Anti-Pattern (VREFCA Stub Resonance)**

* **Symptom:** Unpowered continuity tests pass flawlessly, but the module exhibits highly erratic behavior or total failure during later L3 training phases on the motherboard.  
* **Likely Root Cause:** The tester relied entirely on the CAD software's Design Rule Check (DRC) to confirm electrical connectivity. A planar trace may physically connect the VREFCA (analog reference) plane to the target DRAM pin, satisfying the software. However, if the associated crucial decoupling capacitor is located on a long, inductive "stub" branch rather than directly overlapping the via, the high-speed reference voltage will oscillate wildly under dynamic load.  
* **How to Catch it Early:** L1 continuity testing must transcend simple connection verification; it must verify that the lowest-impedance path to ground routes strictly *through* the decoupling capacitor, rather than past it.  
* **Evidence Proving it is Fixed:** High-magnification physical layout screenshots appended directly to the L1 report, explicitly demonstrating that the VREFCA decoupling capacitors are placed immediately adjacent to the BGA pads, completely preventing stub resonance.

**5\. Latent Flux Residue Leakage Paths**

* **Symptom:** The VDD plane passes the initial continuity test immediately after assembly, but begins to show a slow, creeping resistance drop (e.g., from Megohms down to 50 Ohms) after several days of sitting on the bench, causing erratic power supply behavior in Session 2\.  
* **Likely Root Cause:** The use of aggressive, "no-clean" or water-soluble solder fluxes during SMT assembly without adequate post-assembly ultrasonic cleaning. Over time, particularly in humid environments, the flux residue absorbs ambient moisture, turning into a mildly conductive, high-impedance short across the extremely tight clearances of the BGA package or the 0201 decoupling capacitors.  
* **How to Catch it Early:** Always execute a rigorous, multi-stage ultrasonic cleaning process using pure isopropyl alcohol and distilled water immediately following reflow or manual soldering.  
* **Evidence Proving it is Fixed:** A time-lapsed impedance log demonstrating that the planar resistance remains entirely static and deep in the Megohm range over a consecutive 72-hour period in ambient environmental conditions.

#### **Alıntılanan çalışmalar**

1. Why is DRAM still a black box? I'm trying to build an open DDR memory module. (NOT AN EXPERT \- I'm trying to learn it and design it) : r/hardware \- Reddit, erişim tarihi Mart 7, 2026, [https://www.reddit.com/r/hardware/comments/1rkjxj3/why\_is\_dram\_still\_a\_black\_box\_im\_trying\_to\_build/](https://www.reddit.com/r/hardware/comments/1rkjxj3/why_is_dram_still_a_black_box_im_trying_to_build/)  
2. The Open Memory Initiative (OMI) · GitHub, erişim tarihi Mart 7, 2026, [https://github.com/The-Open-Memory-Initiative-OMI](https://github.com/The-Open-Memory-Initiative-OMI)  
3. Open Memory Initiative (OMI) \- an open DDR4 UDIMM reference design | Hacker News, erişim tarihi Mart 7, 2026, [https://news.ycombinator.com/item?id=47248756](https://news.ycombinator.com/item?id=47248756)  
4. OMI Enters Stage 8: Turning a DDR4 UDIMM Schematic Into ..., erişim tarihi Mart 7, 2026, [https://medium.com/@mefe.sensoy/omi-enters-stage-8-turning-a-ddr4-udimm-schematic-into-verifiable-hardware-c6d252b0e1d3](https://medium.com/@mefe.sensoy/omi-enters-stage-8-turning-a-ddr4-udimm-schematic-into-verifiable-hardware-c6d252b0e1d3)  
5. Why is DRAM still a black box? I'm trying to build an open DDR memory module. \- Reddit, erişim tarihi Mart 7, 2026, [https://www.reddit.com/r/opensource/comments/1rknyvh/why\_is\_dram\_still\_a\_black\_box\_im\_trying\_to\_build/](https://www.reddit.com/r/opensource/comments/1rknyvh/why_is_dram_still_a_black_box_im_trying_to_build/)  
6. r/opensource \- Reddit, erişim tarihi Mart 7, 2026, [https://www.reddit.com/r/opensource/](https://www.reddit.com/r/opensource/)  
7. r/opensource \- Reddit, erişim tarihi Mart 7, 2026, [https://www.reddit.com/r/opensource/best/](https://www.reddit.com/r/opensource/best/)  
8. DDR4 UDIMM PCB/layout review request (8GB 1R x8, non-ECC) \- looking for SI/PI-aware constraint feedback : r/PrintedCircuitBoard \- Reddit, erişim tarihi Mart 7, 2026, [https://www.reddit.com/r/PrintedCircuitBoard/comments/1rknd8p/ddr4\_udimm\_pcblayout\_review\_request\_8gb\_1r\_x8/](https://www.reddit.com/r/PrintedCircuitBoard/comments/1rknd8p/ddr4_udimm_pcblayout_review_request_8gb_1r_x8/)  
9. erişim tarihi Ocak 1, 1970, [https://github.com/The-Open-Memory-Initiative-OMI/tree/main/docs/08\_validation\_and\_review](https://github.com/The-Open-Memory-Initiative-OMI/tree/main/docs/08_validation_and_review)  
10. github.com, erişim tarihi Mart 7, 2026, [https://github.com/The-Open-Memory-Initiative-OMI/omi/tree/main/docs/08\_validation\_and\_review](https://github.com/The-Open-Memory-Initiative-OMI/omi/tree/main/docs/08_validation_and_review)  
11. erişim tarihi Ocak 1, 1970, [https://github.com/The-Open-Memory-Initiative-OMI/omi/blob/main/docs/08\_validation\_and\_review/01\_L1\_bench\_electrical.md](https://github.com/The-Open-Memory-Initiative-OMI/omi/blob/main/docs/08_validation_and_review/01_L1_bench_electrical.md)  
12. erişim tarihi Ocak 1, 1970, [https://raw.githubusercontent.com/The-Open-Memory-Initiative-OMI/omi/main/docs/08\_validation\_and\_review/01\_L1\_bench\_electrical.md](https://raw.githubusercontent.com/The-Open-Memory-Initiative-OMI/omi/main/docs/08_validation_and_review/01_L1_bench_electrical.md)
