The-Open-Memory-Initiative-OMI/omi/docs/08_validation_and_review/OMI Stage 8 L0 Playbook Development.md

# **Open Memory Initiative (OMI) Stage 8 Validation: Comprehensive L0 Artifact Integrity Playbook**

## **Executive Overview**

The Open Memory Initiative (OMI) represents a critical paradigm shift within the open-source hardware ecosystem. Over the past decade, open-source engineering has successfully demystified foundational computing components, yielding open instruction set architectures (such as RISC-V), open-source firmware, and entirely transparent system-on-chip (SoC) designs.1 However, system memory has remained a glaring exception. Despite the public availability of JEDEC DDR standards, the practical implementation of a functional memory module (DIMM) operates almost exclusively behind non-disclosure agreements (NDAs), heavily restricted proprietary reference designs, and closely guarded institutional knowledge native to tier-one memory vendors.1 The Open Memory Initiative systematically dismantles this opacity by engineering a complete, end-to-end, publicly reproducible DDR4 Unbuffered DIMM (UDIMM) reference design.2

Operating under a strict, documentation-first engineering methodology, the OMI emphasizes explicit constraints, observable design intent, and fully reproducible validation over performance maximization or commercial viability.3 The v1 hardware target is intentionally constrained to ensure the project can successfully complete the validation loop using commodity hardware: it is an 8 Gigabyte (GB), Single Rank (1R) DDR4 UDIMM utilizing x8 DRAM devices and operating on a 64-bit non-ECC data bus.2 The initiative has successfully frozen its theoretical and "paper design" phases—spanning architecture decisions, block decomposition, and schematic capture—and has now advanced into Stage 8: Validation & Bring-Up Strategy.3

Stage 8 marks the psychological and methodological transition from asserting that a schematic "looks right" to demanding that it "can be proven right" through immutable evidence.3 To prevent the publication of vague, unverified claims, Stage 8 introduces a stringent, non-negotiable "Validation Ladder" consisting of five ascending levels (L0 through L4).2 Each rung on this ladder demands specific, publishable artifacts. The foundational level of this ladder is L0: Artifact Integrity.4

L0 requires incontrovertible, machine-verifiable evidence that the design artifacts are internally consistent before any physical manufacturing or bench validation (L1) occurs.4 It mandates absolute Electrical Rules Check (ERC) sanity, strict 288/288 edge connector pin map integrity, and mathematically precise naming consistency across all byte lanes and per-device nets.4 By adhering to this playbook, an executing engineer can systematically verify the OMI v1 schematic, diagnose foundational architectural errors, and produce a peer-reviewable L0 evidence package without reliance on proprietary dependencies or subjective "black box" methodologies.

**Next 3 Actions for the Executing Engineer:**

1. **Establish the Local Verification Environment:** Clone the frozen Stage 7 schematic repository, verify exact commit hashes, and configure the local EDA tool (e.g., KiCad) and Python environment to execute the automated L0 netlist parsing scripts.  
2. **Execute the L0 Validation Sessions:** Step sequentially through the five execution sessions defined in this playbook, generating the required .rpt, .csv, and .log evidence files that prove ERC sanity, pin map integrity, and byte-lane isolation.  
3. **Compile and Submit the Evidence Package:** Utilize the provided markdown templates to construct the formal L0 Artifact Integrity Report, link the cryptographic hashes of the evidence files, and submit the package for adversarial peer review via a public GitHub Pull Request.

## **1\. Establishment of Current Project Status**

To effectively execute L0 validation, the reviewing engineer must fundamentally understand the current state of the Open Memory Initiative, distinguishing between what is immutably frozen and what is actively under development.

*Note on Uncertainty and Verification:* During the compilation of this analysis, direct automated access to the live repository markdown files (e.g., START\_HERE.md, SCOPE\_V1.md, and the issue tracker) was restricted.7 Consequently, the precise repository structure and PR numbers must be treated with a degree of uncertainty. To mitigate this, the following status assessment is reconstructed directly from authoritative public communications, architectural logs, and engineering declarations published by the project founder.2 **Verification Method:** Before executing this playbook, the engineer must manually navigate to https://github.com/The-Open-Memory-Initiative-OMI/omi/blob/main/START\_HERE.md and cross-reference the commit history to ensure the Stage 7 freeze remains in effect.

The following table details 15 distinct vectors defining where the OMI project stands today, categorized by development stage and supported by public architectural consensus.3

| \# | Project Vector | Current Status | Implication for L0 Validation | Citation Context |
| :---- | :---- | :---- | :---- | :---- |
| **1** | **Primary Objective** | Defined & Active | The project seeks to create a fully reproducible, open-source DDR4 memory module, optimizing for correctness rather than performance. | 1 |
| **2** | **v1 Hardware Capacity** | Frozen | The target is strictly locked to 8 GB. Any schematic deviation indicating higher density fails L0 BOM sanity checks. | 3 |
| **3** | **v1 Hardware Organization** | Frozen | The architecture is strictly Single Rank (1R). Signals reserved for Rank 2 (e.g., CS1\_n, ODT1) must be explicitly handled as No Connects (NC). | 3 |
| **4** | **v1 Component Selection** | Frozen | The design utilizes x8 DRAM devices. This dictates exactly 8 byte lanes, requiring strict naming verification across 8 unique DRAM symbols (U1-U8). | 3 |
| **5** | **v1 Bus Width & ECC** | Frozen | The design is a 64-bit bus, Non-ECC. The 9th byte lane typically reserved for ECC (CB\[0:7\]) must be absent or properly terminated. | 3 |
| **6** | **Stage 5: Architecture** | Complete & Frozen | The baseline DDR4 UDIMM parameters are locked. No architectural redesigns are permitted during the validation phase. | 3 |
| **7** | **Stage 6: Block Decomposition** | Complete & Frozen | Power delivery networks, CA/CLK routing topologies, and DQ/DQS distributions are conceptually finalized. | 3 |
| **8** | **Stage 7: Schematic Capture** | Complete & Frozen | The electronic representation is locked. This frozen schematic is the sole input artifact for the L0 Validation process. | 3 |
| **9** | **Stage 8: Validation Strategy** | Active (In Progress) | The project is actively defining platform selection, BIOS constraints, failure catalogs, and reporting templates. | 3 |
| **10** | **Validation Ladder: L0** | Active | Defining L0 criteria: ERC sanity, pin map integrity (288/288), and strict naming consistency. This playbook satisfies this vector. | 3 |
| **11** | **Validation Ladder: L1** | Pending | Bench electrical checks (continuity, basic rail stability, SPD I2C reads) will commence only after L0 is achieved. | 3 |
| **12** | **Validation Ladder: L2** | Pending | Host enumeration validation (SPD read by the host system, BIOS generating a plausible configuration) awaits physical prototypes. | 3 |
| **13** | **Validation Ladder: L3** | Pending | Memory training completion and OS boot verification. L0 PI/SI schematic errors often manifest here. | 3 |
| **14** | **Validation Ladder: L4** | Pending | Long-term stress, thermal soak, and repeatability testing across varied commodity hardware platforms. | 3 |
| **15** | **Failure Mode Cataloging** | Active | The community is actively compiling "rookie-killer" mistakes regarding PDN decoupling and SI topology constraints to inform the validation scripts. | 3 |

The implications of this status are profound for the executing engineer. Because Stages 5 through 7 are frozen, the engineer's mandate during Stage 8/L0 is not to optimize the design, suggest alternative components, or re-architect the power delivery network.3 The mandate is strictly forensic: to prove mathematically and logically that the frozen Stage 7 schematic artifacts are internally consistent and adhere to the explicit rules of the DDR4 protocol.4

## **2\. Stage 8 Document Map and Verification Architecture**

The transition from schematic capture to physical validation requires a highly structured documentary environment. While direct directory indexing was restricted during research 14, the project's foundational documentation standards and the explicit requirements of the validation ladder dictate a specific file architecture.4 Stage 8 requires artifacts that include platform details, procedural steps, and structured checklists to prevent personality-driven, subjective reviews.4

The following table maps the required directory structure, typically housed under docs/08\_validation\_and\_review/. It details the purpose, utilization, and expected output artifacts for each component necessary to achieve a robust L0 validation lifecycle. If the executing engineer discovers that any of these files are missing from the live repository, they must implement them based on the definitions provided below to ensure the "Credible L0" standard is met.

| File / Directory Path | Definition & Purpose | Usage Methodology | Expected Output Artifact |
| :---- | :---- | :---- | :---- |
| 08\_validation\_and\_review/README.md | The root index for the validation phase. It explicitly outlines the philosophy of the validation ladder (L0-L4), focusing on structural correctness over performance margins. | Serves as the conceptual starting point for any reviewing engineer. It aligns the reviewer with the project's strict correctness-first principles.4 | Conceptual alignment; no direct programmatic output. |
| 08\_validation\_and\_review/validation\_ladder.md | Defines the exact, granular criteria required to pass each level from L0 (Artifact Integrity) through L4 (Stress \+ Soak).4 | Utilized as the ultimate source of truth to determine if a specific validation phase is legally complete according to OMI governance. | A pass/fail rubric against which all validation PRs are measured. |
| 08\_validation\_and\_review/L0\_artifact\_integrity/ | A sub-directory dedicated exclusively to schematic, netlist, and BOM sanity checking.4 | Houses the specific automated scripts, rulesets, and manual checklists required to mathematically prove the schematic is internally consistent. | The foundational working environment for L0 testing. |
| .../L0\_artifact\_integrity/pin\_map\_288.csv | The master canonical reference file. It maps the standard JEDEC DDR4 UDIMM pin definitions to the schematic's edge connector nets.4 | Ingested by automated Python netlist parsers to verify that all 288 pins are accounted for without omissions, floating inputs, or fatal shorts.4 | A boolean pass/fail log output indicating a perfect 288/288 match. |
| .../L0\_artifact\_integrity/naming\_rules.md | Documents the exact Regular Expressions (Regex) and naming conventions required for byte lanes (e.g., DQ\[0:7\]\_U1) and per-device Command/Address nets.4 | Guides manual reviewers and automated CI/CD linters to ensure consistent labeling, physically preventing cross-lane contamination during layout. | A linting report highlighting any non-conforming net names in the schematic. |
| 08\_validation\_and\_review/failure\_modes\_catalog.md | A continuous register of expected "rookie-killer" mistakes, particularly regarding Signal Integrity (SI) topology, Power Delivery Network (PDN) errors, and SPD misconfigurations.3 | Consulted continuously during the L0 and L1 reviews. Engineers actively search the schematic for the known architectural anti-patterns documented here. | Preventative design modifications documented via specific Git commit messages. |
| 08\_validation\_and\_review/scripts/ | Tooling directory containing parsers (e.g., Python scripts utilizing kicad-netlist-reader) for CI/CD artifact integrity verification.4 | Executed locally by the reviewing engineer (and eventually by automated CI actions) to generate machine-readable validation evidence.4 | Execution logs (.log or .json) proving the schematic passed all structural tests. |
| 08\_validation\_and\_review/templates/ | Directory containing the markdown templates for reporting validation success, ensuring uniform data collection.3 | Copied by an engineer into an Issue or PR description to track L0 progress publicly and predictably.3 | A finalized, fully checked markdown document permanently embedded in the Git history. |

This directory structure ensures that validation is treated as a software engineering problem. By decoupling the validation scripts from the schematic itself, the OMI allows independent engineers to audit the *test mechanisms* just as rigorously as the *hardware design*, ensuring that the validation ladder is built on a foundation of verifiable mathematics rather than blind trust.

## **3\. Precise Definition of L0: Artifact Integrity**

L0 is the bedrock of the OMI Validation Ladder. Its primary function is to serve as a preventative gate, ensuring that no physical manufacturing, PCB layout routing, or bench validation (L1) ever occurs on a conceptually flawed design. If a schematic "looks right" to human eyes but contains implicit violations (such as ambiguous return paths or cross-lane signal swapping), these errors will inevitably manifest as highly anomalous, nearly un-debuggable behavior during L2 (host enumeration) or L3 (memory training).4

The OMI explicitly defines L0 success through three non-negotiable pillars: **ERC sanity, pin map integrity (288/288), and naming consistency**.4 To execute this playbook, the engineer must understand the deep technical implications of each pillar.

### **A. ERC Sanity (Electrical Rules Check)**

**Definition:** The schematic must pass the Electronic Design Automation (EDA) tool’s automated Electrical Rules Check with zero unintended violations. This ensures that fundamental electrical laws—such as avoiding multiple power outputs driving the same net, or preventing inputs from floating without a reference—are not broken within the abstract representation of the circuit.4

* **Acceptance Criteria:** The EDA tool must output an explicitly clean report indicating zero errors.  
* **Required Evidence Artifacts:** An exported ERC log file from the EDA tool (e.g., a KiCad .rpt file) showing 0 Errors. Any warnings present in the log must be accompanied by a documented, mathematically sound waiver explaining why the warning is a false positive based specifically on the DDR4 architecture.  
* **Common Failure Modes & Diagnosis:**  
  * *Symptom:* The ERC logs a critical warning: "Pin connected to other pins, but not driven by any pin."  
  * *Diagnosis:* The engineer failed to place explicit power flags on the global VDD, VPP, or VREFCA nets. Consequently, the EDA tool believes the memory modules have no power source, representing a fundamental breakdown in schematic logic.  
  * *Symptom:* The ERC logs a fatal error: "Conflict problem between pins. Two outputs connected."  
  * *Diagnosis:* Output pins from multiple DRAM devices have been tied together erroneously. For example, tying all data strobe (DQS) pins together globally instead of routing them distinctly per individual byte-lane, which would cause an immediate short-circuit upon bidirectional data transmission.

### **B. Pin Map Integrity (288/288)**

**Definition:** A standard DDR4 Unbuffered DIMM interfaces with the host motherboard via a strictly defined 288-pin edge connector. L0 demands absolute mathematical proof that every single one of these 288 pins defined by the JEDEC standard is mapped to the correct, intended net in the schematic, and appropriately terminated, routed, or explicitly marked as unconnected.4

* **Acceptance Criteria:** A 1:1 algorithmic mapping between the schematic's edge connector nets and a known-good standard reference CSV, resulting in zero unmatched pins.  
* **Required Evidence Artifacts:** A generated IPC-D-356 netlist or an automated script-generated report that cross-references the schematic's edge connector component against the reference CSV. The output log must explicitly and unequivocally state: Mapped: 288, Missing: 0, Mismatched: 0\.  
* **Common Failure Modes & Diagnosis:**  
  * *Symptom:* The PI (Power Integrity) collapses during simulation or physical L3 training, despite data lines appearing correct.  
  * *Diagnosis:* Missing ground return paths. The engineer meticulously mapped the signal pins but treated the numerous VSS (Ground) pins on the edge connector as visually redundant, failing to tie several of them to the global ground net. This violates high-speed return-path requirements, causing massive signal reflection. L0 pin mapping catches this before layout begins.  
  * *Symptom:* The EDA tool flags unrouted nets during layout preparation.  
  * *Diagnosis:* NC (No Connect) pins were left entirely floating in a way that violates tool constraints. The engineer failed to place explicit "No Connect" flags on edge connector pins that are reserved or unused in a 1R x8 configuration (e.g., the pins reserved for a second rank like CS1\_n, ODT1, CKE1).

### **C. Naming Consistency (Byte Lanes and Per-Device Nets)**

**Definition:** DDR4 operates on exceptionally tight timing constraints that are strictly bound by physical byte lanes. A 64-bit data bus consists of 8 distinct byte lanes (each comprising 8 DQ signals, a differential DQS pair, and a Data Mask/DBI signal). Naming consistency requires that schematic nets are labeled utilizing a strict convention such that their association with a specific DRAM chip (e.g., U1 through U8) and their specific byte lane is instantly readable by a human and algorithmically parsable by a script.4

* **Acceptance Criteria:** Every data net must conform to a regex pattern that explicitly binds it to a single DRAM identifier. Furthermore, Command/Address (CA) nets must reflect their topological routing intent (e.g., fly-by daisy chaining).  
* **Required Evidence Artifacts:** A netlist parsing script output verifying that nets adhere to the project's regex rules. For example, ensuring that DQ0 through DQ7 exclusively route to DRAM chip U1, and are paired exclusively with DQS0\_t/DQS0\_c.  
* **Common Failure Modes & Diagnosis:**  
  * *Symptom:* Cross-lane routing violations causing complete memory training failure at L3.  
  * *Diagnosis:* DQ8 (which rightfully belongs to Byte Lane 1, bound to DRAM U2) is accidentally wired to a pin on DRAM U1. If net names do not include explicit device or lane identifiers, this critical error easily passes visual inspection. Naming consistency scripts catch this by grouping nets by name and verifying they terminate at only one active silicon target.  
  * *Symptom:* Ambiguous Clock/Command routing leading to severe SI reflections at L1/L2.  
  * *Diagnosis:* Failing to explicitly name the fly-by topology segments. In DDR4, the clock (CK\_t/CK\_c) hits U1, then daisy-chains to U2, and so forth, ending at a termination resistor. If the net is universally named CK\_t everywhere on the schematic, the layout engineer might route it as a star topology (splitting the signal), which destroys the signal integrity. Naming consistency requires segment names like CK\_t\_U1\_U2 to force the correct layout geometry.

### **Proposed Augmentation: The "Credible L0" Standard**

Because high-level definitions can be manipulated or casually waived by impatient engineers, the executing engineer must apply the "Credible L0" standard. Under this proposed rigorous standard, L0 is *not* achieved by merely opening the EDA tool, clicking "Run ERC," and glancing at the pin map.

L0 is only achieved when the engineer produces an immutable, timestamped artifact package containing:

1. The specific Git Commit SHA of the frozen schematic.  
2. The cryptographic hash (e.g., SHA-256) of the generated netlist.  
3. The exact execution script used to parse the netlist.  
4. The script's raw output log.

If an independent, external engineer cannot check out that exact Git commit, run the exact same script command, and independently view the exact same 288/288 pass result on their own machine, the L0 validation is considered **failed** due to a lack of reproducibility.4

## **4\. "What I Need to Learn" Plan: Targeted L0 Prerequisites**

A common failure mode in open-source hardware verification is engineers becoming overwhelmed by the entirety of the stack. Achieving L0 does *not* require deep knowledge of signal integrity (SI) simulation, electromagnetic interference (EMI), vendor IBIS models, or high-speed PCB layout constraints (like trace length matching).2

L0 is fundamentally an exercise in graph theory, logical consistency, Boolean verification, and EDA tool mastery. The following curriculum strictly bounds the required knowledge, focusing only on what is necessary to achieve L0 success. The engineer should master these concepts before beginning the execution sessions.

| Knowledge Domain | Specific Topic | Learning Objective & Required Reading | Verification Metric |
| :---- | :---- | :---- | :---- |
| **Prerequisites** | DDR4 UDIMM Pinout Architecture | **Read:** JEDEC standard overview for 288-pin DDR4 edge connectors. **Objective:** Understand the topology for a 1R x8 module. Distinguish between power inputs (VDD, VPP), reference voltages (VREFCA), the Command/Address (CA) bus, and distinct DQ/DQS byte lanes.2 | The engineer can accurately map the 8 byte lanes (Lane 0 through Lane 7\) to 8 specific DRAM devices without consulting a reference sheet. |
| **Prerequisites** | EDA Tool ERC Mechanics (e.g., KiCad) | **Read:** EDA documentation on Electrical Rules matrices. **Objective:** Understand how the tool categorizes pins (inputs, outputs, bidirectional, power inputs, passive components), and how the connection matrix generates errors when conflicting pins are joined. | The engineer can deliberately force an ERC error on a test schematic (e.g., connecting a power output to a power output) and successfully resolve it using proper flagging. |
| **Core Topics** | OMI Naming Architecture & Constraints | **Read:** naming\_rules.md (or infer from Stage 7 schematic). **Objective:** Master the project's specific string-matching conventions for per-device nets.4 Understand deeply why fly-by topology requires segment-specific naming (e.g., A0\_U1\_U2) to dictate layout geometry. | The engineer can visually inspect a netlist and instantly identify a net name that violates the project's isolation rules. |
| **Core Topics** | Schematic-to-Edge-Map Traceability | **Read:** standard component datasheets for x8 DDR4 BGA packages. **Objective:** Learn how to trace a signal from a specific BGA ball through the schematic hierarchy down to the exact edge connector pin.3 | The engineer can trace DQ35 from the edge connector, identify that it belongs to Byte Lane 4, and track it to the correct physical pin on component U5. |
| **Core Topics** | BOM Sanity Verification | **Read:** Component instantiation best practices. **Objective:** Ensure every symbol on the schematic has a defined footprint and manufacturer part number compatible with an 8GB 1R x8 module constraint. | The generated Bill of Materials (BOM) CSV contains exactly 8 identical x8 DRAM modules, exactly 1 SPD EEPROM, and matching passives. |
| **Tools** | Netlist Generation & Automated Parsing | **Read:** Python csv and re (regex) module documentation. **Objective:** Learn how to export an IPC-D-356 or standard EDA netlist (e.g., KiCad .net format) and read it programmatically via a script.4 | The engineer can write or execute a simple command-line Python script to extract all nets connected to the DDR4 edge connector symbol and count them. |

## **5\. Step-by-Step Execution Guide to Achieve L0**

This section translates the theoretical L0 requirements into a highly procedural, actionable playbook. The engineer must execute these five sessions sequentially. A failure at any **STOP/GO gate** requires halting execution entirely, diagnosing the error, documenting the deviation, and restarting the current session. **Do not proceed to a subsequent session if the current session fails.**

### **Session 1: Environment Baseline & Sanity Check (30 Minutes)**

* **Goal:** Establish an immutable, verified baseline of the frozen Stage 7 schematic, ensuring that no local modifications, missing libraries, or version mismatches corrupt the validation process.  
* **Exact Actions:**  
  1. Open a terminal and clone the main OMI repository to the local environment: git clone https://github.com/The-Open-Memory-Initiative-OMI/omi.git  
  2. Check out the specific git tag or commit hash designated as the frozen Stage 7 milestone (e.g., git checkout tags/v1-stage7-frozen).  
  3. Launch the designated EDA tool (assuming KiCad 7/8 for open-source workflows) and open the main project file: kicad omi\_v1\_udimm.kicad\_pro.  
  4. Open the schematic editor. Verify that all symbols load correctly without broken link warnings.  
  5. Execute the BOM generation tool from the schematic editor, or via CLI: kicad-cli sch export bom omi\_v1\_udimm.kicad\_sch \-o evidence/session1\_bom.csv.  
  6. Export the raw netlist for later parsing: kicad-cli sch export netlist omi\_v1\_udimm.kicad\_sch \-o evidence/session1\_baseline.net.  
* **Expected Outputs:** A clean, warning-free instantiation of the schematic canvas. A BOM file containing exactly 8 main DRAM chips and 1 SPD chip. A fully populated .net file.  
* **Verification Method:** Open the session1\_bom.csv in a spreadsheet or via grep. Search for the DRAM part number.  
  * *Branch Logic:* If the BOM lists 16 DRAM chips, the schematic is configured for a 2 Rank (2R) module or a 2Rx8 configuration, violating the explicit v1 1R x8 constraint.2  
* **Evidence to Capture:** Commit the generated netlist and BOM to a local tracking folder named evidence/.  
* **STOP/GO Gate:** If the EDA tool reports missing symbol libraries upon opening, **STOP**. Resolve all library paths (Preferences \> Manage Symbol Libraries) before proceeding. Do not validate a broken schematic. If the schematic opens cleanly and the BOM shows exactly 8 DRAMs, **GO**.

### **Session 2: Electrical Rule Check (ERC) Discipline (45 Minutes)**

* **Goal:** Prove that the schematic adheres strictly to electronic logic rules, with zero unintended violations or floating inputs.4  
* **Exact Actions:**  
  1. Navigate to the EDA tool's ERC configuration matrix (Inspect \> Electrical Rules Checker).  
  2. Ensure the violation severity matrix is set to standard strictness. (e.g., Bidirectional connected to Power Output is allowed, but Power Output connected to Power Output is an Error).  
  3. Click Run ERC to execute the tool across the entire schematic hierarchy.  
  4. Review the output log meticulously.  
  5. For every generated error or warning, click the item to trace the coordinate in the schematic.  
  6. Fix actual structural errors (e.g., missing junctions, floating inputs).  
  7. For false-positive warnings inherent to the design, right-click the warning and place an explicit EDA waiver (e.g., an ERC exclusion flag). You *must* add a text note explaining the rationale (e.g., "Waiver: Pin CKE1 is reserved for Rank 2\. Intentionally left floating per JEDEC 1R specs").  
* **Expected Outputs:** An ERC dialog box showing 0 Errors and 0 Unwaived Warnings.  
* **Verification Method:** Re-run the ERC tool after all fixes and waivers are applied to ensure a completely clean pass. Alternatively, run via CLI to generate the immutable report: kicad-cli sch erc omi\_v1\_udimm.kicad\_sch \--output evidence/session2\_erc\_clean.rpt.  
* **Evidence to Capture:** Save the final ERC report as evidence/session2\_erc\_clean.rpt. Take a screenshot of the empty ERC violation dialog window.  
* **STOP/GO Gate:** If there are *any* unresolved or unwaived ERC warnings remaining, **STOP**. L0 cannot be claimed if the design tool indicates a structural flaw. The schematic is not "proven right." If the report is perfectly clean, **GO**.

### **Session 3: Edge Connector Pin Map Verification (60 Minutes)**

* **Goal:** Mathematically prove that all 288 pins on the module's edge connector are accounted for, mapped to the correct JEDEC definitions, and not accidentally floating or shorted to the wrong domain.4  
* **Exact Actions:**  
  1. Locate the automated verification script in the repository (e.g., docs/08\_validation\_and\_review/scripts/verify\_pinmap.py).  
     * *Branch Logic:* If the automated script is absent or failing due to environment issues, the engineer must export the schematic netlist to a CSV and use spreadsheet functions (VLOOKUP) to manually cross-reference the edge connector pins against the known JEDEC standard.  
  2. Acquire the "Known Good" JEDEC DDR4 UDIMM pin map (typically provided in the repo as pin\_map\_288.csv).  
  3. Execute the verification script against the generated schematic netlist in the terminal:  
     python3 verify\_pinmap.py \--netlist evidence/session1\_baseline.net \--reference pin\_map\_288.csv \> evidence/session3\_pinmap\_288\_pass.log  
  4. Analyze the terminal output. The script must check for:  
     * Pins mapped to standard names (e.g., Pin 1 \-\> 12V\_A, Pin 145 \-\> 12V\_B).  
     * Missing pins (pins physically present on the symbol with no net attached).  
     * Shorts (e.g., script detects that VDD and VSS are accidentally assigned to the same physical pin number).  
* **Expected Outputs:** A console output or log file ending with explicit confirmation: STATUS: PASS. 288 pins mapped, matched, and verified.  
* **Verification Method:** To prove the script actually works, deliberately break a connection on the edge connector in the schematic (e.g., delete the wire to pin 50, VSS). Re-export the netlist, run the script, and verify the script catches the error and outputs a FAIL. Revert the deletion afterward.  
* **Evidence to Capture:** Save the execution log as evidence/session3\_pinmap\_288\_pass.log.  
* **STOP/GO Gate:** If the script reports Missing: 1, Mismatched: 3, or any deviation from 288/288, **STOP**. Trace the specific failing pins in the schematic, correct the routing, re-export the netlist, and repeat. If exactly 288/288 match, **GO**.

### **Session 4: Byte Lane and Per-Device Naming Audit (90 Minutes)**

* **Goal:** Verify that naming consistency rules are strictly followed across byte lanes and individual DRAM device nets.4 This ensures that physical routing (Stage 9/Layout) will not suffer from crossed signals or topology flattening.  
* **Exact Actions:**  
  1. Utilize a script (e.g., verify\_naming.py) or manual regex extraction (grep) to pull all data nets (DQ, DQS, DM\_n/DBI\_n) from session1\_baseline.net.  
  2. Group them logically into the 8 required byte lanes based on their schematic names:  
     * Lane 0: DQ\[0:7\], DQS0\_c, DQS0\_t, DM0\_n \-\> Verify regex binds these exclusively to DRAM U1.  
     * Lane 1: DQ\[8:15\], DQS1\_c, DQS1\_t, DM1\_n \-\> Verify regex binds these exclusively to DRAM U2.  
     * ...  
     * Lane 7: DQ\[56:63\], DQS7\_c, DQS7\_t, DM7\_n \-\> Verify regex binds these exclusively to DRAM U8.  
  3. Execute an audit to ensure no net from Lane 0 touches any pin on U2 through U8.  
  4. Verify the CA/CLK bus fly-by naming. Ensure that the clock net between the edge connector and U1 is named distinctly from the clock net between U1 and U2 (e.g., CK\_t\_in vs CK\_t\_U1\_U2). This establishes the required daisy-chain topology intent for the layout engine.  
* **Expected Outputs:** A comprehensive mapping matrix (CSV) proving absolute isolation between byte lanes and explicitly defined fly-by segments.  
* **Verification Method:** Use the EDA tool's "Highlight Net" feature. Click on DQ14. Visually confirm the highlight only illuminates the trace connecting the edge connector to the single specific DRAM chip (U2), without branching to any other component on the board.  
* **Evidence to Capture:** Generate a net-to-component matrix report (via script or EDA export). Save as evidence/session4\_naming\_consistency\_audit.csv.  
* **STOP/GO Gate:** If a single DQ net highlights multiple DRAM chips simultaneously, **STOP**. This represents a catastrophic short circuit across byte lanes. Resolve the naming error in the schematic. If all lanes are isolated properly, **GO**.

### **Session 5: Package Assembly and Sign-off (30 Minutes)**

* **Goal:** Compile the disparate evidence gathered in Sessions 1-4 into the formalized, peer-reviewable L0 Artifact Integrity Report.  
* **Exact Actions:**  
  1. Create a new markdown file named L0\_Validation\_Report\_YYYYMMDD.md.  
  2. Fill out the L0 Report Template (provided in Section 6 of this playbook).  
  3. Link the evidence files (.csv, .rpt, .log) captured in the previous sessions.  
  4. Draft a Pull Request (PR) or GitHub Issue containing the report to formally request an adversarial peer review.  
* **Expected Outputs:** A highly professional, undeniable L0 evidence package.3

## ---

**6\. Deliverable Templates**

To ensure standardization across the open-source community and explicitly avoid "personality-driven" reviews where engineers rely on reputation rather than proof 4, the executing engineer must utilize the following strict markdown templates when submitting L0 evidence.

### **Template A: L0 Report (Markdown)**

# **OMI Stage 8 Validation: L0 Artifact Integrity Report**

**Executing Engineer:** \[GitHub Handle/Name\]

**Date:**

**Target Milestone / Commit Hash:**

## **1\. Executive Summary**

This report presents the immutable evidence required to fulfill Level 0 (L0) validation criteria for the OMI v1 target (DDR4 UDIMM, 8GB, 1R, x8, Non-ECC). All structural, mapping, and naming integrity checks have been executed against the frozen schematic and have passed unequivocally.

## **2\. Check Results & Evidence Verification**

| Check Category | Validation Criteria | Status | Cryptographic Hash (SHA-256) | Evidence File |
| :---- | :---- | :---- | :---- | :---- |
| **BOM Sanity** | 8x DRAM (x8 org), 1x SPD EEPROM | PASS | \[Insert Hash\] | evidence/session1\_bom.csv |
| **ERC Sanity** | 0 Errors, 0 Unwaived Warnings | PASS | \[Insert Hash\] | evidence/session2\_erc\_clean.rpt |
| **Pin Map** | 288/288 Edge Connector match | PASS | \[Insert Hash\] | evidence/session3\_pinmap\_288\_pass.log |
| **Naming** | Byte-lane isolation, Per-device nets | PASS | \[Insert Hash\] | evidence/session4\_naming\_consistency\_audit.csv |

## **3\. Deviations & Documented Waivers**

*The following explicit waivers were applied during the ERC audit. Engineering justifications are provided for peer review.*

* **Waiver 1:** Net CKE1 throws an unconnected warning.  
  * **Justification:** Pin is defined as Clock Enable for Rank 2\. Because the v1 spec is strictly 1R, this pin is explicitly defined as NC (No Connect) per JEDEC DDR4 UDIMM specifications. Waiver applied in EDA tool to prevent false failures.

## **4\. Evidence Package Links**

### **Template B: Review Checklist (Markdown)**

*This template is to be used by a second, independent engineer reviewing the submitted L0 report.*

# **L0 Peer Review & Adversarial Sign-off Checklist**

**Reviewing Engineer:** \[Name/Handle\]

**Reviewing Target Commit:** \[Hash\]

## **Artifact Reproducibility Verification**

* \[ \] **State Replication:** I successfully cloned the repository and checked out the exact commit hash specified in the report.  
* \[ \] **ERC Verification:** I executed the ERC protocol in my local EDA environment and achieved the identical 0 Errors result shown in the submitter's report.  
* \[ \] **Script Verification:** I ran the verify\_pinmap.py script locally and independently confirm the 288/288 pass result.  
* \[ \] **Waiver Audit:** I aggressively reviewed the waivers listed in Section 3 of the L0 report. The engineering justifications provided are mathematically and electrically sound for a DDR4 UDIMM architecture.

## **Visual & Logical Sanity Audit**

* \[ \] **Lane Isolation:** I manually utilized the EDA tool's net highlighting feature on at least one random DQ net per byte lane. I confirmed absolute isolation to a single DRAM component with no cross-talk to other chips.  
* \[ \] **Power Sanity:** I confirmed that the primary power nets (VDD, VPP, and VREFCA) are treated as global domains and are properly distributed to all required logic components, including the SPD EEPROM.

**Final Determination:**

**Comments/Findings:**

### **Template C: Issue/PR Update Format**

### **Stage 8 Progression: L0 Artifact Integrity Completed**

**Context:** The OMI project is systematically advancing through the Stage 8 Validation Ladder. This PR finalizes the foundational L0 (Artifact Integrity) requirement, formally transitioning the Stage 7 schematic from "looks right" visual data into "proven right" mathematically verifiable data.3

**What is included in this PR payload:**

1. Cleaned, final schematic files featuring explicitly waived and documented ERC markers.  
2. The verify\_pinmap.py script alongside the canonical pin\_map\_288.csv reference document.  
3. The formalized L0 Validation Report, linked directly to the immutable evidence logs.

**Next Steps (L1 Readiness):** Upon formal peer approval of this PR, the validation team will proceed to Level 1 (L1: Bench Electrical). This subsequent phase will utilize this proven schematic to generate the physical PCB layout, produce the bare boards, and initiate bench continuity and power rail stability testing.6

## **7\. L0-Specific Risk Register: "Rookie-Killer" Mistakes**

The OMI founder specifically mandated the adversarial review of assumptions and the formal identification of "rookie-killer" pitfalls—mistakes that allow a schematic to look entirely plausible to a casual reviewer but cause the physical module to collapse under training loads or platform variance.2

In the specific context of L0 validation, these risks do not manifest as smoking components; they manifest as logical flaws that bypass visual inspection but fundamentally corrupt the artifact integrity. If these are not caught at L0, they will cost thousands of dollars in wasted prototype manufacturing during L1/L2. The engineer executing L0 must actively hunt for the following specific risks during the ERC and Naming audit sessions.

| Risk ID | Failure Mode / Post-Manufacturing Symptom | Schematic Root Cause | L0 Diagnosis & Early Catch Mechanism | Verification Evidence Required |
| :---- | :---- | :---- | :---- | :---- |
| **R-L0-01** | **Implicit Power Net Aliasing** The schematic passes basic ERC, but the physical board fails to enumerate at L2 because the SPD EEPROM has no power. | The EDA symbol used for the SPD EEPROM has "hidden" power pins implicitly tied to an invisible net named VCC. However, the DDR4 UDIMM standard provides power via a specific pin named VDDSPD. Because the symbol's power pin is hidden, the ERC doesn't flag a disconnected input, but the layout tool leaves it entirely unrouted. | **Catch:** Force the EDA tool to display all hidden pins on all symbols during Session 2\. Manually audit the SPD symbol specifically. | **Evidence:** A screenshot of the SPD symbol in the schematic showing explicitly wired, visible VDDSPD and VSS connections. |
| **R-L0-02** | **Byte Lane Swapping vs. Bit Swapping** The module fails at L3 (Training/Boot) because the memory controller cannot align the data eyes.6 | In DDR routing, swapping data bits *within* a single byte lane (e.g., swapping DQ0 and DQ1) is permissible to ease PCB trace routing. However, the engineer erroneously swapped signals *across* byte lanes (e.g., DQ0 swapped with DQ8), or swapped a DQ with a DQS (strobe) signal. | **Catch:** The Naming Consistency Audit (Session 4). If DQ\[0:7\] routing rules are strictly enforced by the regex script, cross-lane swaps will throw an immediate parsing error. | **Evidence:** The Naming Audit CSV showing strict integer bounding for each U1-U8 byte lane mapping, proving zero cross-contamination. |
| **R-L0-03** | **Decoupling Capacitor Aliasing** The module experiences severe Power Integrity (PI) collapse and voltage droop during heavy read/write loads.4 | To save space on the schematic sheet, the engineer lumped all 50 decoupling capacitors into a single conceptual block in the corner, connected simply to VDD and VSS. Consequently, the layout engineer does not know which specific capacitor belongs to which physical DRAM chip. | **Catch:** Ensure decoupling capacitors are grouped logically adjacent to the specific DRAM symbol they serve. Utilize specific schematic text notes or hierarchical sub-sheets to bind physical layout constraints directly to schematic intent. | **Evidence:** Schematic review notes proving capacitors are localized per DRAM block, not pooled globally. |
| **R-L0-04** | **Fly-by Topology Flattening** Command/Address signals reflect massively, causing complete enumeration failure at L2.13 | The CA bus is drawn as a generic, simplified bus (e.g., net A0 connects to all 8 DRAMs in a star topology). DDR4 strictly requires a fly-by topology, routing sequentially through the chips and terminating at a VTT resistor. | **Catch:** The naming rules check (Session 4). If the CA bus nets are not sequentially segmented (e.g., A0\_U1, A0\_U2), the schematic fails to mandate the fly-by layout to the autorouter or layout engineer. | **Evidence:** A script output verifying that Command/Address nets are daisy-chained with unique net segment names and explicitly terminate at the final VTT block. |
| **R-L0-05** | **Alert\_n and Reset\_n Pull-up Omissions** The module holds the host memory controller in a perpetual wait state, preventing boot. | Critical control signals like ALERT\_n or RESET\_n are mapped directly from the edge connector to the DRAM chips without necessary pull-up resistors to VDD, violating JEDEC open-drain initialization states. | **Catch:** Manual review of the control logic block during the ERC sanity check. Ensure the EDA tool flags outputs tied together without pull-ups. | **Evidence:** The generated BOM explicitly listing the specific pull-up resistors required for open-drain or initialization signals. |

## **Conclusion**

The methodological transition from Stage 7 (Schematic Capture) to Stage 8 (Validation & Bring-Up) represents the most critical engineering juncture in the Open Memory Initiative. By replacing the subjective metric of "looks right" with the rigorous, mathematical, and evidence-backed requirements of the Validation Ladder, the OMI ensures that the open-source community receives a functional, highly reproducible asset.3

Executing Level 0 (Artifact Integrity) is not merely a bureaucratic formality; it is the absolute mathematical and logical bedrock upon which all subsequent physical validation phases (L1 through L4) depend. Without L0, physical validation is largely an exercise in debugging invisible schematic errors. By rigorously applying the steps defined in this playbook, strictly utilizing the standardized templates, and actively hunting and mitigating the specific DDR4 architectural risks outlined in the register, an executing engineer can confidently prove that the OMI v1 schematic is structurally sound. This L0 success definitively establishes artifact integrity and clears the path for the project to advance to the physical manufacturing bench.

#### **Alıntılanan çalışmalar**

1. Why is DRAM still a black box? I'm trying to build an open DDR memory module. (NOT AN EXPERT \- I'm trying to learn it and design it) : r/hardware \- Reddit, erişim tarihi Mart 5, 2026, [https://www.reddit.com/r/hardware/comments/1rkjxj3/why\_is\_dram\_still\_a\_black\_box\_im\_trying\_to\_build/](https://www.reddit.com/r/hardware/comments/1rkjxj3/why_is_dram_still_a_black_box_im_trying_to_build/)  
2. Open Memory Initiative (OMI) \- an open DDR4 UDIMM reference design | Hacker News, erişim tarihi Mart 5, 2026, [https://news.ycombinator.com/item?id=47248756](https://news.ycombinator.com/item?id=47248756)  
3. DDR4 UDIMM PCB/layout review request (8GB 1R x8, non-ECC) \- looking for SI/PI-aware constraint feedback : r/PrintedCircuitBoard \- Reddit, erişim tarihi Mart 5, 2026, [https://www.reddit.com/r/PrintedCircuitBoard/comments/1rknd8p/ddr4\_udimm\_pcblayout\_review\_request\_8gb\_1r\_x8/](https://www.reddit.com/r/PrintedCircuitBoard/comments/1rknd8p/ddr4_udimm_pcblayout_review_request_8gb_1r_x8/)  
4. OMI Enters Stage 8: Turning a DDR4 UDIMM Schematic Into Verifiable Hardware \- Medium, erişim tarihi Mart 5, 2026, [https://medium.com/@mefe.sensoy/omi-enters-stage-8-turning-a-ddr4-udimm-schematic-into-verifiable-hardware-c6d252b0e1d3](https://medium.com/@mefe.sensoy/omi-enters-stage-8-turning-a-ddr4-udimm-schematic-into-verifiable-hardware-c6d252b0e1d3)  
5. Why is DRAM still a black box? I'm trying to build an open DDR memory module. \- Reddit, erişim tarihi Mart 5, 2026, [https://www.reddit.com/r/opensource/comments/1rknyvh/why\_is\_dram\_still\_a\_black\_box\_im\_trying\_to\_build/](https://www.reddit.com/r/opensource/comments/1rknyvh/why_is_dram_still_a_black_box_im_trying_to_build/)  
6. r/opensource \- Reddit, erişim tarihi Mart 5, 2026, [https://www.reddit.com/r/opensource/best/](https://www.reddit.com/r/opensource/best/)  
7. erişim tarihi Ocak 1, 1970, [https://github.com/The-Open-Memory-Initiative-OMI/blob/main/README.md](https://github.com/The-Open-Memory-Initiative-OMI/blob/main/README.md)  
8. github.com, erişim tarihi Mart 5, 2026, [https://github.com/The-Open-Memory-Initiative-OMI/omi/blob/main/SCOPE\_V1.md](https://github.com/The-Open-Memory-Initiative-OMI/omi/blob/main/SCOPE_V1.md)  
9. github.com, erişim tarihi Mart 5, 2026, [https://github.com/The-Open-Memory-Initiative-OMI/omi/blob/main/START\_HERE.md](https://github.com/The-Open-Memory-Initiative-OMI/omi/blob/main/START_HERE.md)  
10. github.com, erişim tarihi Mart 5, 2026, [https://github.com/The-Open-Memory-Initiative-OMI/omi/issues](https://github.com/The-Open-Memory-Initiative-OMI/omi/issues)  
11. Mert Efe Şensoy mertefesensoy \- GitHub, erişim tarihi Mart 5, 2026, [https://github.com/mertefesensoy](https://github.com/mertefesensoy)  
12. r/PrintedCircuitBoard \- Reddit, erişim tarihi Mart 5, 2026, [https://www.reddit.com/r/PrintedCircuitBoard/](https://www.reddit.com/r/PrintedCircuitBoard/)  
13. r/PrintedCircuitBoard \- Reddit, erişim tarihi Mart 5, 2026, [https://www.reddit.com/r/PrintedCircuitBoard/new/](https://www.reddit.com/r/PrintedCircuitBoard/new/)  
14. github.com, erişim tarihi Mart 5, 2026, [https://github.com/The-Open-Memory-Initiative-OMI/omi/tree/main/docs/08\_validation\_and\_review](https://github.com/The-Open-Memory-Initiative-OMI/omi/tree/main/docs/08_validation_and_review)  
15. Official Printed Circuit Board (PCB) Subreddit, erişim tarihi Mart 5, 2026, [https://www.reddit.com/r/PrintedCircuitBoard/hot/](https://www.reddit.com/r/PrintedCircuitBoard/hot/)
