The-Open-Memory-Initiative-OMI/omi/docs/08_validation_and_review/templates/L1_peer_review_checklist.md

# L1 Peer Review & Adversarial Sign-off Checklist

**Reviewing Engineer:** [Name / Handle]
**Reviewing Target Commit:** [Git SHA]
**L1 Report Under Review:** [link to PR or report file]
**Review Date:** YYYY-MM-DD

---

## Measurement Log Verification

- [ ] **Completeness:** I verified that the measurement log CSV contains
      entries for all functional pins (all non-NC pins from the 288-pin map).

- [ ] **Validator Execution:** I ran `validate_continuity_log.py` against
      the submitted measurement log and my results match the submitter's
      `continuity_report.json`.

- [ ] **Hash Verification:** I computed SHA-256 hashes of the input files
      (pin map CSV, measurement log CSV) and they match the hashes in the
      L1 evidence package.

---

## GND & Power Verification

- [ ] **GND Resistance Spot-Check:** I spot-checked at least 10 GND/VSS
      pins in the measurement log and confirmed all show ≤1 Ω resistance.

- [ ] **Power Rail Continuity:** I verified that the measurement log shows
      continuity within each power rail (VDD, VPP, VDDSPD, VTT, VREF).

- [ ] **Rail Isolation:** I confirmed that rail-to-rail isolation measurements
      exist for all critical pairs (VDD↔VPP, VDD↔VDDSPD, VDD↔GND, etc.)
      and all show ≥10 kΩ.

- [ ] **Rail Voltage (if applicable):** I verified powered rail voltage
      measurements are within spec (VDD=1.2V±5%, VPP=2.5V±5%,
      VDDSPD=2.2-3.6V, VTT≈VDD/2, VREF≈VDD/2).

---

## Signal Integrity Spot-Check

- [ ] **DQ Lane Sampling:** I spot-checked at least 1 DQ pin per byte lane
      (8 lanes total) in the measurement log and confirmed continuity
      to the DRAM device.

- [ ] **CA/CLK Sampling:** I spot-checked at least 3 CA/CLK signals
      (e.g., RESET_n pin 58, CKE0 pin 60, CK_t pin 74) and confirmed
      continuity.

- [ ] **NC Isolation Sampling:** I spot-checked at least 5 NC pins
      and confirmed ≥1 MΩ isolation (no shorts to adjacent pins).

---

## SPD Bus Verification

- [ ] **SPD Continuity:** I verified the measurement log shows continuity
      for SCL (pin 141), SDA (pin 285), SA0 (pin 139), SA1 (pin 140),
      SA2 (pin 238), and VDDSPD (pin 284) to the SPD EEPROM.

- [ ] **Waveform Evidence (if applicable):** I reviewed oscilloscope
      captures of SCL/SDA and confirmed pull-up waveform shape is
      consistent with I2C open-drain topology.

---

## Evidence Package Audit

- [ ] **Scope/DVM Screenshots:** I reviewed the attached measurement
      screenshots and they are consistent with the reported values.

- [ ] **Waiver Review:** I reviewed the waivers listed in the L1 report.
      The engineering justifications are electrically sound for a DDR4
      UDIMM 1R x8 non-ECC architecture.

---

## Final Determination

**Review Result:** PASS / FAIL / NEEDS REVISION

**Comments / Findings:**

> [Provide detailed findings here. If FAIL or NEEDS REVISION, list specific
> items that must be corrected before L1 can be approved.]

---

**Signed:** [Reviewer Name / Handle]
**Date:** YYYY-MM-DD
