The-Open-Memory-Initiative-OMI/omi/design/power/omi_v1_power/omi_v1_power.kicad_pcb

## KiCad design blueprint/PCB/LeoIoT_Goalfinder.kicad_pcb



Board: 2 copper layers, 100.0 x 50.0 mm, 41 parts (15 on the bottom side), 22 nets.

Parts:
C1: 22µF; CP_Radial_D5.0mm_P2.00mm
C2: 4,7µF; CP_Radial_D5.0mm_P2.00mm
C3, C4, C5, C6, C8, C9: 100nF; C_0805_2012Metric_Pad1.18x1.45mm_HandSolder
Copt3, Copt4, Copt5, Copt6, Copt8, Copt9: 100nF; C_Disc_D5.0mm_W2.5mm_P2.50mm
J1: USB in; PinHeader_1x04_P2.54mm_Vertical
J2: USB-ESP; PinHeader_1x04_P2.54mm_Vertical
J3: GAIN; PinHeader_2x05_P2.54mm_Vertical
J4: LED Strip; JST_XH_B2B-XH-A_1x02_P2.54mm_Vertical
J7: LIS3DH; PinHeader_1x06_P2.54mm_Horizontal
LS1: Speaker; Mono-Enclosed_Speaker_70x30x17mm_onboard
MH1, MH2, MH3, MH3#2, MH4: MountingHole_3.2mm_M3
Q1: IRLML2502; SOT-23
Qopt1: IRLML2502; TO-220-3_Horizontal_TabDown
R1, R2, R3: 100k; R_0805_2012Metric_Pad1.20x1.40mm_HandSolder
R4: 1k; R_0805_2012Metric_Pad1.20x1.40mm_HandSolder
R5: 33k; R_0805_2012Metric_Pad1.20x1.40mm_HandSolder
Ropt1, Ropt2, Ropt3: 100k; R_Axial_DIN0309_L9.0mm_D3.2mm_P12.70mm_Horizontal
Ropt4: 1k; R_Axial_DIN0309_L9.0mm_D3.2mm_P12.70mm_Horizontal
Ropt5: 33k; R_Axial_DIN0309_L9.0mm_D3.2mm_P12.70mm_Horizontal
U1: ESP32 D1 Mini; ESP32_D1_mini
U2: VL53L0X - ToF; VL53L0X_Breakout_Board_vertical_flat
U3: MAX98357A - Amplifier; MAX98357A_Breakout_Board
U4: SW240 - Vcc/D0/GND; SW420_Breakout_Board_Horizontal

Connections:
3V3: C5.1, C6.1, C8.1, C9.1, Copt5.1, Copt6.1, Copt8.1, Copt9.1, J7.1, R3.1, Ropt3.1, U1.16 (3V3), U2.1 (VCC), U4.3
5V: C1.1, C2.1, C3.1, C4.1, Copt3.1, Copt4.1, J1.1, J2.1, J3.3, J4.1, R1.1, Ropt1.1, U3.7 (VDD)
/LED_PWR: J4.2, Q1.3 (D), Qopt1.2 (S)
GND: C1.2, C2.2, C3.2, C4.2, C5.2, C6.2, C8.2, C9.2, Copt3.2, Copt4.2, Copt5.2, Copt6.2, Copt8.2, Copt9.2, J1.4, J2.4, J3.7, J7.2, Q1.2 (S), Qopt1.3 (D), R2.1, R5.2, Ropt2.1, Ropt5.2, U1.1 (GND), U1.22 (GND), U1.33 (GND), U2.2 (GND), U3.6 (GND), U4.2
unnamed: J1.2, J2.2
unnamed: J1.3, J2.3
unnamed: J3.1, R1.2, Ropt1.2
unnamed: J3.9, R2.2, Ropt2.2
unnamed: U1.18 (IO_13/TCK), U4.1
unnamed: U1.27 (IO_21/SDA_1), U2.3 (SDA)
unnamed: U1.25 (IO_22/SCL_1), U2.4 (SCL)
unnamed: J7.3, U1.31 (IO_16/U2_RX)
unnamed: J7.4, U1.32 (IO_04)
unnamed: J7.5, R3.2, Ropt3.2
unnamed: J7.6, U1.30 (IO_12/TDI)
unnamed: Q1.1 (G), Qopt1.1 (G), R4.2, R5.1, Ropt4.2
unnamed: U1.14 (IO_05/SS), U3.1 (LRCLK)
unnamed: R4.1, Ropt4.1, Ropt5.1, U1.29 (IO_17/U2_TXC)
unnamed: U1.8 (IO_18/CLK), U3.5 (~SD_MODE)
unnamed: U1.10 (IO_19/MISO), U3.3 (DIN)
unnamed: U1.12 (IO_23/MOSI), U3.2 (BCLK)
unnamed: J3.2, J3.4, J3.6, J3.8, J3.10, U3.4 (GAIN_SLOT)
