The-Open-Memory-Initiative-OMI/omi/design/power/omi_v1_power/omi_v1_power.kicad_pcb

## KiCad design blueprint/PCB/LeoIoT_Goalfinder_r1.4_SMD.kicad_pcb



Board: 2 copper layers, 70.0 x 40.1 mm, 27 parts (13 on the bottom side), 20 nets.

Parts:
C1: 22µF; CP_Radial_D5.0mm_P2.00mm
C2: 4,7µF; CP_Radial_D5.0mm_P2.00mm
C3, C4, C5, C6, C8, C9: 100nF; C_0805_2012Metric_Pad1.18x1.45mm_HandSolder
J1: USB in; PinHeader_1x04_P2.54mm_Vertical
J2: USB-ESP; PinHeader_1x04_P2.54mm_Vertical
J4: LED Strip; JST_XH_B2B-XH-A_1x02_P2.50mm_Vertical
J5: SW240 - Vcc/D0/GND; PinHeader_1x03_P2.54mm_Horizontal
J6: VL53L0X-ToF Vcc/SDA/SCL/GND; PinHeader_1x04_P2.54mm_Vertical
LS1: Speaker; Mono-Enclosed_Speaker_70x30x17mm_onboard
MH1, MH2, MH3, MH4: MountingHole_3.2mm_M3
Q1: IRLML2502; SOT-23
R2, R3: 100k; R_0805_2012Metric_Pad1.20x1.40mm_HandSolder
R4: 1k; R_0805_2012Metric_Pad1.20x1.40mm_HandSolder
R5: 33k; R_0805_2012Metric_Pad1.20x1.40mm_HandSolder
U1: ESP32 D1 Mini; ESP32_D1_mini
U2: VL53L0X - ToF; VL53L0X_Breakout_Board_vertical_flat
U3: MAX98357A - Amplifier; MAX98357A_Breakout_Board
U5: LIS3DH - Accelerometer; LIS3DH_Breakout_Board

Connections:
3V3: C5.1, C6.1, C8.1, C9.1, J5.1, J6.1, R3.1, U1.16 (3V3), U2.1 (VCC), U5.1 (VCC)
5V: C1.1, C2.1, C3.1, C4.1, J1.1, J2.1, J4.1, U3.7 (VDD)
/LED_PWR: J4.2, Q1.3 (D)
GND: C1.2, C2.2, C3.2, C4.2, C5.2, C6.2, C8.2, C9.2, J1.4, J2.4, J5.3, J6.4, Q1.2 (S), R2.1, R5.2, U1.1 (GND), U1.22 (GND), U1.33 (GND), U2.2 (GND), U3.6 (GND), U5.2 (GND)
unnamed: J1.2, J2.2
unnamed: J1.3, J2.3
unnamed: J5.2, U1.18 (IO_13/TCK)
unnamed: J6.2, U1.27 (IO_21/SDA_1), U2.3 (SDA)
unnamed: J6.3, U1.25 (IO_22/SCL_1), U2.4 (SCL)
unnamed: U1.31 (IO_16/U2_RX), U5.3 (SCL/SPC)
unnamed: U1.32 (IO_04), U5.4 (SDA/SDI/SDO)
unnamed: R3.2, U5.6 (CS)
unnamed: U1.30 (IO_12/TDI), U5.7 (INT1)
unnamed: Q1.1 (G), R4.2, R5.1
unnamed: U1.14 (IO_05/SS), U3.1 (LRCLK)
unnamed: R4.1, U1.29 (IO_17/U2_TXC)
unnamed: U1.8 (IO_18/CLK), U3.5 (~SD_MODE)
unnamed: U1.10 (IO_19/MISO), U3.3 (DIN)
unnamed: U1.12 (IO_23/MOSI), U3.2 (BCLK)
unnamed: R2.2, U3.4 (GAIN_SLOT)
